sofiapanag/Shipwars-IoT-ESE-516/Code main/Code_main/WINC1500_HTTP_DOWNLOADER_EXAMPLE1/src/IMU/lsm6dso_reg.c

/**
  ******************************************************************************
  * @file    lsm6dso_reg.c
  * @author  Sensors Software Solution Team
  * @brief   LSM6DSO driver file
  ******************************************************************************
  * @attention
  *
  * <h2><center>&copy; Copyright (c) 2021 STMicroelectronics.
  * All rights reserved.</center></h2>
  *
  * This software component is licensed by ST under BSD 3-Clause license,
  * the "License"; You may not use this file except in compliance with the
  * License. You may obtain a copy of the License at:
  *                        opensource.org/licenses/BSD-3-Clause
  *
  ******************************************************************************
  */

#include "lsm6dso_reg.h"
#include "I2cDriver\I2cDriver.h"
#include <stddef.h>

/**
  * @defgroup  LSM6DSO
  * @brief     This file provides a set of functions needed to drive the
  *            lsm6dso enhanced inertial module.
  * @{
  *
  */

/**
  * @defgroup  LSM6DSO_Interfaces_Functions
  * @brief     This section provide a set of functions used to read and
  *            write a generic register of the device.
  *            MANDATORY: return 0 -> no Error.
  * @{
  *
  */

/**
  * @brief  Read generic device register
  *
  * @param  ctx   read / write interface definitions(ptr)
  * @param  reg   register to read
  * @param  data  pointer to buffer that store the data read(ptr)
  * @param  len   number of consecutive register to read
  * @retval          interface status (MANDATORY: return 0 -> no Error)
  *
  */
int32_t lsm6dso_read_reg(stmdev_ctx_t *ctx, uint8_t reg,
                         uint8_t *data,
                         uint16_t len)
{
  int32_t ret;

  ret = ctx->read_reg(ctx->handle, reg, data, len);

  return ret;
}

/**
  * @brief  Write generic device register
  *
  * @param  ctx   read / write interface definitions(ptr)
  * @param  reg   register to write
  * @param  data  pointer to data to write in register reg(ptr)
  * @param  len   number of consecutive register to write
  * @retval          interface status (MANDATORY: return 0 -> no Error)
  *
  */
int32_t lsm6dso_write_reg(stmdev_ctx_t *ctx, uint8_t reg,
                          uint8_t *data,
                          uint16_t len)
{
  int32_t ret;

  ret = ctx->write_reg(ctx->handle, reg, data, len);

  return ret;
}

/**
  * @}
  *
  */

/**
  * @defgroup  LSM6DSOX_Private_functions
  * @brief     Section collect all the utility functions needed by APIs.
  * @{
  *
  */

static void bytecpy(uint8_t *target, uint8_t *source)
{
  if ((target != NULL) && (source != NULL))
  {
    *target = *source;
  }
}

/**
  * @defgroup  LSM6DSO_Sensitivity
  * @brief     These functions convert raw-data into engineering units.
  * @{
  *
  */
float_t lsm6dso_from_fs2_to_mg(int16_t lsb)
{
  return ((float_t)lsb) * 0.061f;
}

float_t lsm6dso_from_fs4_to_mg(int16_t lsb)
{
  return ((float_t)lsb) * 0.122f;
}

float_t lsm6dso_from_fs8_to_mg(int16_t lsb)
{
  return ((float_t)lsb) * 0.244f;
}

float_t lsm6dso_from_fs16_to_mg(int16_t lsb)
{
  return ((float_t)lsb) * 0.488f;
}

float_t lsm6dso_from_fs125_to_mdps(int16_t lsb)
{
  return ((float_t)lsb) * 4.375f;
}

float_t lsm6dso_from_fs500_to_mdps(int16_t lsb)
{
  return ((float_t)lsb) * 17.50f;
}

float_t lsm6dso_from_fs250_to_mdps(int16_t lsb)
{
  return ((float_t)lsb) * 8.750f;
}

float_t lsm6dso_from_fs1000_to_mdps(int16_t lsb)
{
  return ((float_t)lsb) * 35.0f;
}

float_t lsm6dso_from_fs2000_to_mdps(int16_t lsb)
{
  return ((float_t)lsb) * 70.0f;
}

float_t lsm6dso_from_lsb_to_celsius(int16_t lsb)
{
  return (((float_t)lsb / 256.0f) + 25.0f);
}

float_t lsm6dso_from_lsb_to_nsec(int16_t lsb)
{
  return ((float_t)lsb * 25000.0f);
}

/**
  * @}
  *
  */

/**
  * @defgroup  LSM6DSO_Data_Generation
  * @brief     This section groups all the functions concerning
  *            data generation.
  *
  */

/**
  * @brief  Accelerometer full-scale selection.[set]
  *
  * @param  ctx      read / write interface definitions
  * @param  val      change the values of fs_xl in reg CTRL1_XL
  * @retval             interface status (MANDATORY: return 0 -> no Error)
  *
  */
int32_t lsm6dso_xl_full_scale_set(stmdev_ctx_t *ctx,
                                  lsm6dso_fs_xl_t val)
{
  lsm6dso_ctrl1_xl_t reg;
  int32_t ret;

  ret = lsm6dso_read_reg(ctx, LSM6DSO_CTRL1_XL, (uint8_t *)&reg, 1);

  if (ret == 0)
  {
    reg.fs_xl = (uint8_t) val;
    ret = lsm6dso_write_reg(ctx, LSM6DSO_CTRL1_XL, (uint8_t *)&reg, 1);
  }

  return ret;
}

/**
  * @brief  Accelerometer full-scale selection.[get]
  *
  * @param  ctx      read / write interface definitions
  * @param  val      Get the values of fs_xl in reg CTRL1_XL
  * @retval             interface status (MANDATORY: return 0 -> no Error)
  *
  */
int32_t lsm6dso_xl_full_scale_get(stmdev_ctx_t *ctx,
                                  lsm6dso_fs_xl_t *val)
{
  lsm6dso_ctrl1_xl_t reg;
  int32_t ret;

  ret = lsm6dso_read_reg(ctx, LSM6DSO_CTRL1_XL, (uint8_t *)&reg, 1);

  switch (reg.fs_xl)
  {
    case LSM6DSO_2g:
      *val = LSM6DSO_2g;
      break;

    case LSM6DSO_16g:
      *val = LSM6DSO_16g;
      break;

    case LSM6DSO_4g:
      *val = LSM6DSO_4g;
      break;

    case LSM6DSO_8g:
      *val = LSM6DSO_8g;
      break;

    default:
      *val = LSM6DSO_2g;
      break;
  }

  return ret;
}

/**
  * @brief  Accelerometer UI data rate selection.[set]
  *
  * @param  ctx      read / write interface definitions
  * @param  val      change the values of odr_xl in reg CTRL1_XL
  * @retval             interface status (MANDATORY: return 0 -> no Error)
  *
  */
int32_t lsm6dso_xl_data_rate_set(stmdev_ctx_t *ctx,
                                 lsm6dso_odr_xl_t val)
{
  lsm6dso_odr_xl_t odr_xl =  val;
  lsm6dso_emb_fsm_enable_t fsm_enable;
  lsm6dso_fsm_odr_t fsm_odr;
  lsm6dso_ctrl1_xl_t reg;
  int32_t ret;

  /* Check the Finite State Machine data rate constraints */
  ret =  lsm6dso_fsm_enable_get(ctx, &fsm_enable);

  if (ret == 0)
  {
    if ((fsm_enable.fsm_enable_a.fsm1_en  |
         fsm_enable.fsm_enable_a.fsm2_en  |
         fsm_enable.fsm_enable_a.fsm3_en  |
         fsm_enable.fsm_enable_a.fsm4_en  |
         fsm_enable.fsm_enable_a.fsm5_en  |
         fsm_enable.fsm_enable_a.fsm6_en  |
         fsm_enable.fsm_enable_a.fsm7_en  |
         fsm_enable.fsm_enable_a.fsm8_en  |
         fsm_enable.fsm_enable_b.fsm9_en  |
         fsm_enable.fsm_enable_b.fsm10_en |
         fsm_enable.fsm_enable_b.fsm11_en |
         fsm_enable.fsm_enable_b.fsm12_en |
         fsm_enable.fsm_enable_b.fsm13_en |
         fsm_enable.fsm_enable_b.fsm14_en |
         fsm_enable.fsm_enable_b.fsm15_en |
         fsm_enable.fsm_enable_b.fsm16_en) == PROPERTY_ENABLE)
    {
      ret =  lsm6dso_fsm_data_rate_get(ctx, &fsm_odr);

      if (ret == 0)
      {
        switch (fsm_odr)
        {
          case LSM6DSO_ODR_FSM_12Hz5:
            if (val == LSM6DSO_XL_ODR_OFF)
            {
              odr_xl = LSM6DSO_XL_ODR_12Hz5;
            }

            else
            {
              odr_xl = val;
            }

            break;

          case LSM6DSO_ODR_FSM_26Hz:
            if (val == LSM6DSO_XL_ODR_OFF)
            {
              odr_xl = LSM6DSO_XL_ODR_26Hz;
            }

            else if (val == LSM6DSO_XL_ODR_12Hz5)
            {
              odr_xl = LSM6DSO_XL_ODR_26Hz;
            }

            else
            {
              odr_xl = val;
            }

            break;

          case LSM6DSO_ODR_FSM_52Hz:
            if (val == LSM6DSO_XL_ODR_OFF)
            {
              odr_xl = LSM6DSO_XL_ODR_52Hz;
            }

            else if (val == LSM6DSO_XL_ODR_12Hz5)
            {
              odr_xl = LSM6DSO_XL_ODR_52Hz;
            }

            else if (val == LSM6DSO_XL_ODR_26Hz)
            {
              odr_xl = LSM6DSO_XL_ODR_52Hz;
            }

            else
            {
              odr_xl = val;
            }

            break;

          case LSM6DSO_ODR_FSM_104Hz:
            if (val == LSM6DSO_XL_ODR_OFF)
            {
              odr_xl = LSM6DSO_XL_ODR_104Hz;
            }

            else if (val == LSM6DSO_XL_ODR_12Hz5)
            {
              odr_xl = LSM6DSO_XL_ODR_104Hz;
            }

            else if (val == LSM6DSO_XL_ODR_26Hz)
            {
              odr_xl = LSM6DSO_XL_ODR_104Hz;
            }

            else if (val == LSM6DSO_XL_ODR_52Hz)
            {
              odr_xl = LSM6DSO_XL_ODR_104Hz;
            }

            else
            {
              odr_xl = val;
            }

            break;

          default:
            odr_xl = val;
            break;
        }
      }
    }
  }

  if (ret == 0)
  {
    ret = lsm6dso_read_reg(ctx, LSM6DSO_CTRL1_XL, (uint8_t *)&reg, 1);
  }

  if (ret == 0)
  {
    reg.odr_xl = (uint8_t) odr_xl;
    ret = lsm6dso_write_reg(ctx, LSM6DSO_CTRL1_XL, (uint8_t *)&reg, 1);
  }

  return ret;
}

/**
  * @brief  Accelerometer UI data rate selection.[get]
  *
  * @param  ctx      read / write interface definitions
  * @param  val      Get the values of odr_xl in reg CTRL1_XL
  * @retval             interface status (MANDATORY: return 0 -> no Error)
  *
  */
int32_t lsm6dso_xl_data_rate_get(stmdev_ctx_t *ctx,
                                 lsm6dso_odr_xl_t *val)
{
  lsm6dso_ctrl1_xl_t reg;
  int32_t ret;

  ret = lsm6dso_read_reg(ctx, LSM6DSO_CTRL1_XL, (uint8_t *)&reg, 1);

  switch (reg.odr_xl)
  {
    case LSM6DSO_XL_ODR_OFF:
      *val = LSM6DSO_XL_ODR_OFF;
      break;

    case LSM6DSO_XL_ODR_12Hz5:
      *val = LSM6DSO_XL_ODR_12Hz5;
      break;

    case LSM6DSO_XL_ODR_26Hz:
      *val = LSM6DSO_XL_ODR_26Hz;
      break;

    case LSM6DSO_XL_ODR_52Hz:
      *val = LSM6DSO_XL_ODR_52Hz;
      break;

    case LSM6DSO_XL_ODR_104Hz:
      *val = LSM6DSO_XL_ODR_104Hz;
      break;

    case LSM6DSO_XL_ODR_208Hz:
      *val = LSM6DSO_XL_ODR_208Hz;
      break;

    case LSM6DSO_XL_ODR_417Hz:
      *val = LSM6DSO_XL_ODR_417Hz;
      break;

    case LSM6DSO_XL_ODR_833Hz:
      *val = LSM6DSO_XL_ODR_833Hz;
      break;

    case LSM6DSO_XL_ODR_1667Hz:
      *val = LSM6DSO_XL_ODR_1667Hz;
      break;

    case LSM6DSO_XL_ODR_3333Hz:
      *val = LSM6DSO_XL_ODR_3333Hz;
      break;

    case LSM6DSO_XL_ODR_6667Hz:
      *val = LSM6DSO_XL_ODR_6667Hz;
      break;

    case LSM6DSO_XL_ODR_1Hz6:
      *val = LSM6DSO_XL_ODR_1Hz6;
      break;

    default:
      *val = LSM6DSO_XL_ODR_OFF;
      break;
  }

  return ret;
}

/**
  * @brief  Gyroscope UI chain full-scale selection.[set]
  *
  * @param  ctx      read / write interface definitions
  * @param  val      change the values of fs_g in reg CTRL2_G
  * @retval             interface status (MANDATORY: return 0 -> no Error)
  *
  */
int32_t lsm6dso_gy_full_scale_set(stmdev_ctx_t *ctx,
                                  lsm6dso_fs_g_t val)
{
  lsm6dso_ctrl2_g_t reg;
  int32_t ret;

  ret = lsm6dso_read_reg(ctx, LSM6DSO_CTRL2_G, (uint8_t *)&reg, 1);

  if (ret == 0)
  {
    reg.fs_g = (uint8_t) val;
    ret = lsm6dso_write_reg(ctx, LSM6DSO_CTRL2_G, (uint8_t *)&reg, 1);
  }

  return ret;
}

/**
  * @brief  Gyroscope UI chain full-scale selection.[get]
  *
  * @param  ctx      read / write interface definitions
  * @param  val      Get the values of fs_g in reg CTRL2_G
  * @retval             interface status (MANDATORY: return 0 -> no Error)
  *
  */
int32_t lsm6dso_gy_full_scale_get(stmdev_ctx_t *ctx,
                                  lsm6dso_fs_g_t *val)
{
  lsm6dso_ctrl2_g_t reg;
  int32_t ret;

  ret = lsm6dso_read_reg(ctx, LSM6DSO_CTRL2_G, (uint8_t *)&reg, 1);

  switch (reg.fs_g)
  {
    case LSM6DSO_250dps:
      *val = LSM6DSO_250dps;
      break;

    case LSM6DSO_125dps:
      *val = LSM6DSO_125dps;
      break;

    case LSM6DSO_500dps:
      *val = LSM6DSO_500dps;
      break;

    case LSM6DSO_1000dps:
      *val = LSM6DSO_1000dps;
      break;

    case LSM6DSO_2000dps:
      *val = LSM6DSO_2000dps;
      break;

    default:
      *val = LSM6DSO_250dps;
      break;
  }

  return ret;
}

/**
  * @brief  Gyroscope UI data rate selection.[set]
  *
  * @param  ctx      read / write interface definitions
  * @param  val      change the values of odr_g in reg CTRL2_G
  * @retval             interface status (MANDATORY: return 0 -> no Error)
  *
  */
int32_t lsm6dso_gy_data_rate_set(stmdev_ctx_t *ctx,
                                 lsm6dso_odr_g_t val)
{
  lsm6dso_odr_g_t odr_gy =  val;
  lsm6dso_emb_fsm_enable_t fsm_enable;
  lsm6dso_fsm_odr_t fsm_odr;
  lsm6dso_ctrl2_g_t reg;
  int32_t ret;

  /* Check the Finite State Machine data rate constraints */
  ret =  lsm6dso_fsm_enable_get(ctx, &fsm_enable);

  if (ret == 0)
  {
    if ((fsm_enable.fsm_enable_a.fsm1_en  |
         fsm_enable.fsm_enable_a.fsm2_en  |
         fsm_enable.fsm_enable_a.fsm3_en  |
         fsm_enable.fsm_enable_a.fsm4_en  |
         fsm_enable.fsm_enable_a.fsm5_en  |
         fsm_enable.fsm_enable_a.fsm6_en  |
         fsm_enable.fsm_enable_a.fsm7_en  |
         fsm_enable.fsm_enable_a.fsm8_en  |
         fsm_enable.fsm_enable_b.fsm9_en  |
         fsm_enable.fsm_enable_b.fsm10_en |
         fsm_enable.fsm_enable_b.fsm11_en |
         fsm_enable.fsm_enable_b.fsm12_en |
         fsm_enable.fsm_enable_b.fsm13_en |
         fsm_enable.fsm_enable_b.fsm14_en |
         fsm_enable.fsm_enable_b.fsm15_en |
         fsm_enable.fsm_enable_b.fsm16_en) == PROPERTY_ENABLE)
    {
      ret =  lsm6dso_fsm_data_rate_get(ctx, &fsm_odr);

      if (ret == 0)
      {
        switch (fsm_odr)
        {
          case LSM6DSO_ODR_FSM_12Hz5:
            if (val == LSM6DSO_GY_ODR_OFF)
            {
              odr_gy = LSM6DSO_GY_ODR_12Hz5;
            }

            else
            {
              odr_gy = val;
            }

            break;

          case LSM6DSO_ODR_FSM_26Hz:
            if (val == LSM6DSO_GY_ODR_OFF)
            {
              odr_gy = LSM6DSO_GY_ODR_26Hz;
            }

            else if (val == LSM6DSO_GY_ODR_12Hz5)
            {
              odr_gy = LSM6DSO_GY_ODR_26Hz;
            }

            else
            {
              odr_gy = val;
            }

            break;

          case LSM6DSO_ODR_FSM_52Hz:
            if (val == LSM6DSO_GY_ODR_OFF)
            {
              odr_gy = LSM6DSO_GY_ODR_52Hz;
            }

            else if (val == LSM6DSO_GY_ODR_12Hz5)
            {
              odr_gy = LSM6DSO_GY_ODR_52Hz;
            }

            else if (val == LSM6DSO_GY_ODR_26Hz)
            {
              odr_gy = LSM6DSO_GY_ODR_52Hz;
            }

            else
            {
              odr_gy = val;
            }

            break;

          case LSM6DSO_ODR_FSM_104Hz:
            if (val == LSM6DSO_GY_ODR_OFF)
            {
              odr_gy = LSM6DSO_GY_ODR_104Hz;
            }

            else if (val == LSM6DSO_GY_ODR_12Hz5)
            {
              odr_gy = LSM6DSO_GY_ODR_104Hz;
            }

            else if (val == LSM6DSO_GY_ODR_26Hz)
            {
              odr_gy = LSM6DSO_GY_ODR_104Hz;
            }

            else if (val == LSM6DSO_GY_ODR_52Hz)
            {
              odr_gy = LSM6DSO_GY_ODR_104Hz;
            }

            else
            {
              odr_gy = val;
            }

            break;

          default:
            odr_gy = val;
            break;
        }
      }
    }
  }

  if (ret == 0)
  {
    ret = lsm6dso_read_reg(ctx, LSM6DSO_CTRL2_G, (uint8_t *)&reg, 1);
  }

  if (ret == 0)
  {
    reg.odr_g = (uint8_t) odr_gy;
    ret = lsm6dso_write_reg(ctx, LSM6DSO_CTRL2_G, (uint8_t *)&reg, 1);
  }

  return ret;
}

/**
  * @brief  Gyroscope UI data rate selection.[get]
  *
  * @param  ctx      read / write interface definitions
  * @param  val      Get the values of odr_g in reg CTRL2_G
  * @retval             interface status (MANDATORY: return 0 -> no Error)
  *
  */
int32_t lsm6dso_gy_data_rate_get(stmdev_ctx_t *ctx,
                                 lsm6dso_odr_g_t *val)
{
  lsm6dso_ctrl2_g_t reg;
  int32_t ret;

  ret = lsm6dso_read_reg(ctx, LSM6DSO_CTRL2_G, (uint8_t *)&reg, 1);

  switch (reg.odr_g)
  {
    case LSM6DSO_GY_ODR_OFF:
      *val = LSM6DSO_GY_ODR_OFF;
      break;

    case LSM6DSO_GY_ODR_12Hz5:
      *val = LSM6DSO_GY_ODR_12Hz5;
      break;

    case LSM6DSO_GY_ODR_26Hz:
      *val = LSM6DSO_GY_ODR_26Hz;
      break;

    case LSM6DSO_GY_ODR_52Hz:
      *val = LSM6DSO_GY_ODR_52Hz;
      break;

    case LSM6DSO_GY_ODR_104Hz:
      *val = LSM6DSO_GY_ODR_104Hz;
      break;

    case LSM6DSO_GY_ODR_208Hz:
      *val = LSM6DSO_GY_ODR_208Hz;
      break;

    case LSM6DSO_GY_ODR_417Hz:
      *val = LSM6DSO_GY_ODR_417Hz;
      break;

    case LSM6DSO_GY_ODR_833Hz:
      *val = LSM6DSO_GY_ODR_833Hz;
      break;

    case LSM6DSO_GY_ODR_1667Hz:
      *val = LSM6DSO_GY_ODR_1667Hz;
      break;

    case LSM6DSO_GY_ODR_3333Hz:
      *val = LSM6DSO_GY_ODR_3333Hz;
      break;

    case LSM6DSO_GY_ODR_6667Hz:
      *val = LSM6DSO_GY_ODR_6667Hz;
      break;

    default:
      *val = LSM6DSO_GY_ODR_OFF;
      break;
  }

  return ret;
}

/**
  * @brief  Block data update.[set]
  *
  * @param  ctx      read / write interface definitions
  * @param  val      change the values of bdu in reg CTRL3_C
  * @retval             interface status (MANDATORY: return 0 -> no Error)
  *
  */
int32_t lsm6dso_block_data_update_set(stmdev_ctx_t *ctx, uint8_t val)
{
  lsm6dso_ctrl3_c_t reg;
  int32_t ret;

  ret = lsm6dso_read_reg(ctx, LSM6DSO_CTRL3_C, (uint8_t *)&reg, 1);

  if (ret == 0)
  {
    reg.bdu = val;
    ret = lsm6dso_write_reg(ctx, LSM6DSO_CTRL3_C, (uint8_t *)&reg, 1);
  }

  return ret;
}

/**
  * @brief  Block data update.[get]
  *
  * @param  ctx      read / write interface definitions
  * @param  val      change the values of bdu in reg CTRL3_C
  * @retval             interface status (MANDATORY: return 0 -> no Error)
  *
  */
int32_t lsm6dso_block_data_update_get(stmdev_ctx_t *ctx, uint8_t *val)
{
  lsm6dso_ctrl3_c_t reg;
  int32_t ret;

  ret = lsm6dso_read_reg(ctx, LSM6DSO_CTRL3_C, (uint8_t *)&reg, 1);
  *val = reg.bdu;

  return ret;
}

/**
  * @brief  Weight of XL user offset bits of registers X_OFS_USR (73h),
  *         Y_OFS_USR (74h), Z_OFS_USR (75h).[set]
  *
  * @param  ctx      read / write interface definitions
  * @param  val      change the values of usr_off_w in reg CTRL6_C
  * @retval             interface status (MANDATORY: return 0 -> no Error)
  *
  */
int32_t lsm6dso_xl_offset_weight_set(stmdev_ctx_t *ctx,
                                     lsm6dso_usr_off_w_t val)
{
  lsm6dso_ctrl6_c_t reg;
  int32_t ret;

  ret = lsm6dso_read_reg(ctx, LSM6DSO_CTRL6_C, (uint8_t *)&reg, 1);

  if (ret == 0)
  {
    reg.usr_off_w = (uint8_t)val;
    ret = lsm6dso_write_reg(ctx, LSM6DSO_CTRL6_C, (uint8_t *)&reg, 1);
  }

  return ret;
}

/**
  * @brief    Weight of XL user offset bits of registers X_OFS_USR (73h),
  *           Y_OFS_USR (74h), Z_OFS_USR (75h).[get]
  *
  * @param    ctx      read / write interface definitions
  * @param    val      Get the values of usr_off_w in reg CTRL6_C
  * @retval             interface status (MANDATORY: return 0 -> no Error)
  *
  */
int32_t lsm6dso_xl_offset_weight_get(stmdev_ctx_t *ctx,
                                     lsm6dso_usr_off_w_t *val)
{
  lsm6dso_ctrl6_c_t reg;
  int32_t ret;

  ret = lsm6dso_read_reg(ctx, LSM6DSO_CTRL6_C, (uint8_t *)&reg, 1);

  switch (reg.usr_off_w)
  {
    case LSM6DSO_LSb_1mg:
      *val = LSM6DSO_LSb_1mg;
      break;

    case LSM6DSO_LSb_16mg:
      *val = LSM6DSO_LSb_16mg;
      break;

    default:
      *val = LSM6DSO_LSb_1mg;
      break;
  }

  return ret;
}

/**
  * @brief  Accelerometer power mode.[set]
  *
  * @param  ctx      read / write interface definitions
  * @param  val      change the values of xl_hm_mode in
  *                               reg CTRL6_C
  * @retval             interface status (MANDATORY: return 0 -> no Error)
  *
  */
int32_t lsm6dso_xl_power_mode_set(stmdev_ctx_t *ctx,
                                  lsm6dso_xl_hm_mode_t val)
{
  lsm6dso_ctrl5_c_t ctrl5_c;
  lsm6dso_ctrl6_c_t ctrl6_c;
  int32_t ret;

  ret = lsm6dso_read_reg(ctx, LSM6DSO_CTRL5_C, (uint8_t *) &ctrl5_c, 1);

  if (ret == 0)
  {
    ctrl5_c.xl_ulp_en = ((uint8_t)val & 0x02U) >> 1;
    ret = lsm6dso_write_reg(ctx, LSM6DSO_CTRL5_C, (uint8_t *) &ctrl5_c, 1);
  }

  if (ret == 0)
  {
    ret = lsm6dso_read_reg(ctx, LSM6DSO_CTRL6_C, (uint8_t *) &ctrl6_c, 1);
  }

  if (ret == 0)
  {
    ctrl6_c.xl_hm_mode = (uint8_t)val & 0x01U;
    ret = lsm6dso_write_reg(ctx, LSM6DSO_CTRL6_C, (uint8_t *) &ctrl6_c, 1);
  }

  return ret;
}

/**
  * @brief  Accelerometer power mode.[get]
  *
  * @param  ctx      read / write interface definitions
  * @param  val      Get the values of xl_hm_mode in reg CTRL6_C
  * @retval             interface status (MANDATORY: return 0 -> no Error)
  *
  */
int32_t lsm6dso_xl_power_mode_get(stmdev_ctx_t *ctx,
                                  lsm6dso_xl_hm_mode_t *val)
{
  lsm6dso_ctrl5_c_t ctrl5_c;
  lsm6dso_ctrl6_c_t ctrl6_c;
  int32_t ret;

  ret = lsm6dso_read_reg(ctx, LSM6DSO_CTRL5_C, (uint8_t *) &ctrl5_c, 1);

  if (ret == 0)
  {
    ret = lsm6dso_read_reg(ctx, LSM6DSO_CTRL6_C, (uint8_t *) &ctrl6_c, 1);

    switch ((ctrl5_c.xl_ulp_en << 1) | ctrl6_c.xl_hm_mode)
    {
      case LSM6DSO_HIGH_PERFORMANCE_MD:
        *val = LSM6DSO_HIGH_PERFORMANCE_MD;
        break;

      case LSM6DSO_LOW_NORMAL_POWER_MD:
        *val = LSM6DSO_LOW_NORMAL_POWER_MD;
        break;

      case LSM6DSO_ULTRA_LOW_POWER_MD:
        *val = LSM6DSO_ULTRA_LOW_POWER_MD;
        break;

      default:
        *val = LSM6DSO_HIGH_PERFORMANCE_MD;
        break;
    }
  }

  return ret;
}

/**
  * @brief  Operating mode for gyroscope.[set]
  *
  * @param  ctx      read / write interface definitions
  * @param  val      change the values of g_hm_mode in reg CTRL7_G
  * @retval             interface status (MANDATORY: return 0 -> no Error)
  *
  */
int32_t lsm6dso_gy_power_mode_set(stmdev_ctx_t *ctx,
                                  lsm6dso_g_hm_mode_t val)
{
  lsm6dso_ctrl7_g_t reg;
  int32_t ret;

  ret = lsm6dso_read_reg(ctx, LSM6DSO_CTRL7_G, (uint8_t *)&reg, 1);

  if (ret == 0)
  {
    reg.g_hm_mode = (uint8_t)val;
    ret = lsm6dso_write_reg(ctx, LSM6DSO_CTRL7_G, (uint8_t *)&reg, 1);
  }

  return ret;
}

/**
  * @brief  Operating mode for gyroscope.[get]
  *
  * @param  ctx      read / write interface definitions
  * @param  val      Get the values of g_hm_mode in reg CTRL7_G
  * @retval             interface status (MANDATORY: return 0 -> no Error)
  *
  */
int32_t lsm6dso_gy_power_mode_get(stmdev_ctx_t *ctx,
                                  lsm6dso_g_hm_mode_t *val)
{
  lsm6dso_ctrl7_g_t reg;
  int32_t ret;

  ret = lsm6dso_read_reg(ctx, LSM6DSO_CTRL7_G, (uint8_t *)&reg, 1);

  switch (reg.g_hm_mode)
  {
    case LSM6DSO_GY_HIGH_PERFORMANCE:
      *val = LSM6DSO_GY_HIGH_PERFORMANCE;
      break;

    case LSM6DSO_GY_NORMAL:
      *val = LSM6DSO_GY_NORMAL;
      break;

    default:
      *val = LSM6DSO_GY_HIGH_PERFORMANCE;
      break;
  }

  return ret;
}

/**
  * @brief  The STATUS_REG register is read by the primary interface.[get]
  *
  * @param  ctx      read / write interface definitions
  * @param  val      register STATUS_REG
  * @retval             interface status (MANDATORY: return 0 -> no Error)
  *
  */
int32_t lsm6dso_status_reg_get(stmdev_ctx_t *ctx,
                               lsm6dso_status_reg_t *val)
{
  int32_t ret;

  ret = lsm6dso_read_reg(ctx, LSM6DSO_STATUS_REG, (uint8_t *) val, 1);

  return ret;
}

/**
  * @brief  Accelerometer new data available.[get]
  *
  * @param  ctx      read / write interface definitions
  * @param  val      change the values of xlda in reg STATUS_REG
  * @retval             interface status (MANDATORY: return 0 -> no Error)
  *
  */
int32_t lsm6dso_xl_flag_data_ready_get(stmdev_ctx_t *ctx,
                                       uint8_t *val)
{
  lsm6dso_status_reg_t reg;
  int32_t ret;

  ret = lsm6dso_read_reg(ctx, LSM6DSO_STATUS_REG, (uint8_t *)&reg, 1);
  *val = reg.xlda;

  return ret;
}

/**
  * @brief  Gyroscope new data available.[get]
  *
  * @param  ctx      read / write interface definitions
  * @param  val      change the values of gda in reg STATUS_REG
  * @retval             interface status (MANDATORY: return 0 -> no Error)
  *
  */
int32_t lsm6dso_gy_flag_data_ready_get(stmdev_ctx_t *ctx,
                                       uint8_t *val)
{
  lsm6dso_status_reg_t reg;
  int32_t ret;

  ret = lsm6dso_read_reg(ctx, LSM6DSO_STATUS_REG, (uint8_t *)&reg, 1);
  *val = reg.gda;

  return ret;
}

/**
  * @brief  Temperature new data available.[get]
  *
  * @param  ctx      read / write interface definitions
  * @param  val      change the values of tda in reg STATUS_REG
  * @retval             interface status (MANDATORY: return 0 -> no Error)
  *
  */
int32_t lsm6dso_temp_flag_data_ready_get(stmdev_ctx_t *ctx,
                                         uint8_t *val)
{
  lsm6dso_status_reg_t reg;
  int32_t ret;

  ret = lsm6dso_read_reg(ctx, LSM6DSO_STATUS_REG, (uint8_t *)&reg, 1);
  *val = reg.tda;

  return ret;
}

/**
  * @brief  Accelerometer X-axis user offset correction expressed in
  *         two’s complement, weight depends on USR_OFF_W in CTRL6_C (15h).
  *         The value must be in the range [-127 127].[set]
  *
  * @param  ctx      read / write interface definitions
  * @param  buff     buffer that contains data to write
  * @retval             interface status (MANDATORY: return 0 -> no Error)
  *
  */
int32_t lsm6dso_xl_usr_offset_x_set(stmdev_ctx_t *ctx, uint8_t *buff)
{
  int32_t ret;

  ret = lsm6dso_write_reg(ctx, LSM6DSO_X_OFS_USR, buff, 1);

  return ret;
}

/**
  * @brief  Accelerometer X-axis user offset correction expressed in two’s
  *         complement, weight depends on USR_OFF_W in CTRL6_C (15h).
  *         The value must be in the range [-127 127].[get]
  *
  * @param  ctx      read / write interface definitions
  * @param  buff     buffer that stores data read
  * @retval             interface status (MANDATORY: return 0 -> no Error)
  *
  */
int32_t lsm6dso_xl_usr_offset_x_get(stmdev_ctx_t *ctx, uint8_t *buff)
{
  int32_t ret;

  ret = lsm6dso_read_reg(ctx, LSM6DSO_X_OFS_USR, buff, 1);

  return ret;
}

/**
  * @brief  Accelerometer Y-axis user offset correction expressed in two’s
  *         complement, weight depends on USR_OFF_W in CTRL6_C (15h).
  *         The value must be in the range [-127 127].[set]
  *
  * @param  ctx      read / write interface definitions
  * @param  buff     buffer that contains data to write
  * @retval             interface status (MANDATORY: return 0 -> no Error)
  *
  */
int32_t lsm6dso_xl_usr_offset_y_set(stmdev_ctx_t *ctx, uint8_t *buff)
{
  int32_t ret;

  ret = lsm6dso_write_reg(ctx, LSM6DSO_Y_OFS_USR, buff, 1);

  return ret;
}

/**
  * @brief  Accelerometer Y-axis user offset correction expressed in two’s
  *         complement, weight depends on USR_OFF_W in CTRL6_C (15h).
  *         The value must be in the range [-127 127].[get]
  *
  * @param  ctx      read / write interface definitions
  * @param  buff     buffer that stores data read
  * @retval             interface status (MANDATORY: return 0 -> no Error)
  *
  */
int32_t lsm6dso_xl_usr_offset_y_get(stmdev_ctx_t *ctx, uint8_t *buff)
{
  int32_t ret;

  ret = lsm6dso_read_reg(ctx, LSM6DSO_Y_OFS_USR, buff, 1);

  return ret;
}

/**
  * @brief  Accelerometer Z-axis user offset correction expressed in two’s
  *         complement, weight depends on USR_OFF_W in CTRL6_C (15h).
  *         The value must be in the range [-127 127].[set]
  *
  * @param  ctx      read / write interface definitions
  * @param  buff     buffer that contains data to write
  * @retval             interface status (MANDATORY: return 0 -> no Error)
  *
  */
int32_t lsm6dso_xl_usr_offset_z_set(stmdev_ctx_t *ctx, uint8_t *buff)
{
  int32_t ret;

  ret = lsm6dso_write_reg(ctx, LSM6DSO_Z_OFS_USR, buff, 1);

  return ret;
}

/**
  * @brief  Accelerometer Z-axis user offset correction expressed in two’s
  *         complement, weight depends on USR_OFF_W in CTRL6_C (15h).
  *         The value must be in the range [-127 127].[get]
  *
  * @param  ctx      read / write interface definitions
  * @param  buff     buffer that stores data read
  * @retval             interface status (MANDATORY: return 0 -> no Error)
  *
  */
int32_t lsm6dso_xl_usr_offset_z_get(stmdev_ctx_t *ctx, uint8_t *buff)
{
  int32_t ret;

  ret = lsm6dso_read_reg(ctx, LSM6DSO_Z_OFS_USR, buff, 1);

  return ret;
}

/**
  * @brief  Enables user offset on out.[set]
  *
  * @param  ctx      read / write interface definitions
  * @param  val      change the values of usr_off_on_out in reg CTRL7_G
  * @retval             interface status (MANDATORY: return 0 -> no Error)
  *
  */
int32_t lsm6dso_xl_usr_offset_set(stmdev_ctx_t *ctx, uint8_t val)
{
  lsm6dso_ctrl7_g_t reg;
  int32_t ret;

  ret = lsm6dso_read_reg(ctx, LSM6DSO_CTRL7_G, (uint8_t *)&reg, 1);

  if (ret == 0)
  {
    reg.usr_off_on_out = val;
    ret = lsm6dso_write_reg(ctx, LSM6DSO_CTRL7_G, (uint8_t *)&reg, 1);
  }

  return ret;
}

/**
  * @brief  User offset on out flag.[get]
  *
  * @param  ctx      read / write interface definitions
  * @param  val      values of usr_off_on_out in reg CTRL7_G
  * @retval             interface status (MANDATORY: return 0 -> no Error)
  *
  */
int32_t lsm6dso_xl_usr_offset_get(stmdev_ctx_t *ctx, uint8_t *val)
{
  lsm6dso_ctrl7_g_t reg;
  int32_t ret;

  ret = lsm6dso_read_reg(ctx, LSM6DSO_CTRL7_G, (uint8_t *)&reg, 1);
  *val = reg.usr_off_on_out;

  return ret;
}

/**
  * @}
  *
  */

/**
  * @defgroup  LSM6DSO_Timestamp
  * @brief     This section groups all the functions that manage the
  *            timestamp generation.
  * @{
  *
  */

/**
  * @brief  Reset timestamp counter.[set]
  *
  * @param  ctx    Read / write interface definitions.(ptr)
  * @retval        Interface status (MANDATORY: return 0 -> no Error)
  *
  */
int32_t lsm6dso_timestamp_rst(stmdev_ctx_t *ctx)
{
  uint8_t rst_val = 0xAA;
  return lsm6dso_write_reg(ctx, LSM6DSO_TIMESTAMP2, &rst_val, 1);
}

/**
  * @brief  Enables timestamp counter.[set]
  *
  * @param  ctx      read / write interface definitions
  * @param  val      change the values of timestamp_en in reg CTRL10_C
  * @retval             interface status (MANDATORY: return 0 -> no Error)
  *
  */
int32_t lsm6dso_timestamp_set(stmdev_ctx_t *ctx, uint8_t val)
{
  lsm6dso_ctrl10_c_t reg;
  int32_t ret;

  ret = lsm6dso_read_reg(ctx, LSM6DSO_CTRL10_C, (uint8_t *)&reg, 1);

  if (ret == 0)
  {
    reg.timestamp_en = val;
    ret = lsm6dso_write_reg(ctx, LSM6DSO_CTRL10_C, (uint8_t *)&reg, 1);
  }

  return ret;
}

/**
  * @brief  Enables timestamp counter.[get]
  *
  * @param  ctx      read / write interface definitions
  * @param  val      change the values of timestamp_en in reg CTRL10_C
  * @retval             interface status (MANDATORY: return 0 -> no Error)
  *
  */
int32_t lsm6dso_timestamp_get(stmdev_ctx_t *ctx, uint8_t *val)
{
  lsm6dso_ctrl10_c_t reg;
  int32_t ret;

  ret = lsm6dso_read_reg(ctx, LSM6DSO_CTRL10_C, (uint8_t *)&reg, 1);
  *val = reg.timestamp_en;

  return ret;
}

/**
  * @brief  Timestamp first data output register (r).
  *         The value is expressed as a 32-bit word and the bit
  *         resolution is 25 μs.[get]
  *
  * @param  ctx      read / write interface definitions
  * @param  buff     buffer that stores data read
  * @retval             interface status (MANDATORY: return 0 -> no Error)
  *
  */
int32_t lsm6dso_timestamp_raw_get(stmdev_ctx_t *ctx, uint32_t *val)
{
  uint8_t buff[4];
  int32_t ret;

  ret = lsm6dso_read_reg(ctx, LSM6DSO_TIMESTAMP0, buff, 4);
  *val = buff[3];
  *val = (*val * 256U) +  buff[2];
  *val = (*val * 256U) +  buff[1];
  *val = (*val * 256U) +  buff[0];

  return ret;
}

/**
  * @}
  *
  */

/**
  * @defgroup  LSM6DSO_Data output
  * @brief     This section groups all the data output functions.
  * @{
  *
  */

/**
  * @brief  Circular burst-mode (rounding) read of the output
  *         registers.[set]
  *
  * @param  ctx      read / write interface definitions
  * @param  val      change the values of rounding in reg CTRL5_C
  * @retval             interface status (MANDATORY: return 0 -> no Error)
  *
  */
int32_t lsm6dso_rounding_mode_set(stmdev_ctx_t *ctx,
                                  lsm6dso_rounding_t val)
{
  lsm6dso_ctrl5_c_t reg;
  int32_t ret;

  ret = lsm6dso_read_reg(ctx, LSM6DSO_CTRL5_C, (uint8_t *)&reg, 1);

  if (ret == 0)
  {
    reg.rounding = (uint8_t)val;
    ret = lsm6dso_write_reg(ctx, LSM6DSO_CTRL5_C, (uint8_t *)&reg, 1);
  }

  return ret;
}

/**
  * @brief  Gyroscope UI chain full-scale selection.[get]
  *
  * @param  ctx      read / write interface definitions
  * @param  val      Get the values of rounding in reg CTRL5_C
  * @retval             interface status (MANDATORY: return 0 -> no Error)
  *
  */
int32_t lsm6dso_rounding_mode_get(stmdev_ctx_t *ctx,
                                  lsm6dso_rounding_t *val)
{
  lsm6dso_ctrl5_c_t reg;
  int32_t ret;

  ret = lsm6dso_read_reg(ctx, LSM6DSO_CTRL5_C, (uint8_t *)&reg, 1);

  switch (reg.rounding)
  {
    case LSM6DSO_NO_ROUND:
      *val = LSM6DSO_NO_ROUND;
      break;

    case LSM6DSO_ROUND_XL:
      *val = LSM6DSO_ROUND_XL;
      break;

    case LSM6DSO_ROUND_GY:
      *val = LSM6DSO_ROUND_GY;
      break;

    case LSM6DSO_ROUND_GY_XL:
      *val = LSM6DSO_ROUND_GY_XL;
      break;

    default:
      *val = LSM6DSO_NO_ROUND;
      break;
  }

  return ret;
}

/**
  * @brief  Temperature data output register (r).
  *         L and H registers together express a 16-bit word in two’s
  *         complement.[get]
  *
  * @param  ctx      read / write interface definitions
  * @param  buff     buffer that stores data read
  * @retval             interface status (MANDATORY: return 0 -> no Error)
  *
  */
int32_t lsm6dso_temperature_raw_get(stmdev_ctx_t *ctx, int16_t *val)
{
  uint8_t buff[2];
  int32_t ret;

  ret = lsm6dso_read_reg(ctx, LSM6DSO_OUT_TEMP_L, buff, 2);
  val[0] = (int16_t)buff[1];
  val[0] = (val[0] * 256) + (int16_t)buff[0];

  return ret;
}

/**
  * @brief  Angular rate sensor. The value is expressed as a 16-bit
  *         word in two’s complement.[get]
  *
  * @param  ctx      read / write interface definitions
  * @param  buff     buffer that stores data read
  * @retval             interface status (MANDATORY: return 0 -> no Error)
  *
  */
int32_t lsm6dso_angular_rate_raw_get(stmdev_ctx_t *ctx, int16_t *val)
{
  uint8_t buff[6];
  int32_t ret;

  ret = lsm6dso_read_reg(ctx, LSM6DSO_OUTX_L_G, buff, 6);
  val[0] = (int16_t)buff[1];
  val[0] = (val[0] * 256) + (int16_t)buff[0];
  val[1] = (int16_t)buff[3];
  val[1] = (val[1] * 256) + (int16_t)buff[2];
  val[2] = (int16_t)buff[5];
  val[2] = (val[2] * 256) + (int16_t)buff[4];

  return ret;
}

/**
  * @brief  Linear acceleration output register.
  *         The value is expressed as a 16-bit word in two’s complement.[get]
  *
  * @param  ctx      read / write interface definitions
  * @param  buff     buffer that stores data read
  * @retval             interface status (MANDATORY: return 0 -> no Error)
  *
  */
int32_t lsm6dso_acceleration_raw_get(stmdev_ctx_t *ctx, int16_t *val)
{
  uint8_t buff[6];
  int32_t ret;

  ret = lsm6dso_read_reg(ctx, LSM6DSO_OUTX_L_A, buff, 6);
  val[0] = (int16_t)buff[1];
  val[0] = (val[0] * 256) + (int16_t)buff[0];
  val[1] = (int16_t)buff[3];
  val[1] = (val[1] * 256) + (int16_t)buff[2];
  val[2] = (int16_t)buff[5];
  val[2] = (val[2] * 256) + (int16_t)buff[4];

  return ret;
}

/**
  * @brief  FIFO data output [get]
  *
  * @param  ctx      read / write interface definitions
  * @param  buff     buffer that stores data read
  * @retval             interface status (MANDATORY: return 0 -> no Error)
  *
  */
int32_t lsm6dso_fifo_out_raw_get(stmdev_ctx_t *ctx, uint8_t *buff)
{
  int32_t ret;

  ret = lsm6dso_read_reg(ctx, LSM6DSO_FIFO_DATA_OUT_X_L, buff, 6);

  return ret;
}

/**
  * @brief  Step counter output register.[get]
  *
  * @param  ctx      read / write interface definitions
  * @param  buff     buffer that stores data read
  * @retval             interface status (MANDATORY: return 0 -> no Error)
  *
  */
int32_t lsm6dso_number_of_steps_get(stmdev_ctx_t *ctx, uint16_t *val)
{
  uint8_t buff[2];
  int32_t ret;

  ret = lsm6dso_mem_bank_set(ctx, LSM6DSO_EMBEDDED_FUNC_BANK);

  if (ret == 0)
  {
    ret = lsm6dso_read_reg(ctx, LSM6DSO_STEP_COUNTER_L, buff, 2);
  }

  if (ret == 0)
  {
    *val = buff[1];
    *val = (*val * 256U) +  buff[0];
    ret = lsm6dso_mem_bank_set(ctx, LSM6DSO_USER_BANK);
  }

  return ret;
}

/**
  * @brief  Reset step counter register.[get]
  *
  * @param  ctx      read / write interface definitions
  * @retval             interface status (MANDATORY: return 0 -> no Error)
  *
  */
int32_t lsm6dso_steps_reset(stmdev_ctx_t *ctx)
{
  lsm6dso_emb_func_src_t reg;
  int32_t ret;

  ret = lsm6dso_mem_bank_set(ctx, LSM6DSO_EMBEDDED_FUNC_BANK);

  if (ret == 0)
  {
    ret = lsm6dso_read_reg(ctx, LSM6DSO_EMB_FUNC_SRC, (uint8_t *)&reg, 1);
  }

  if (ret == 0)
  {
    reg.pedo_rst_step = PROPERTY_ENABLE;
    ret = lsm6dso_write_reg(ctx, LSM6DSO_EMB_FUNC_SRC, (uint8_t *)&reg, 1);
  }

  if (ret == 0)
  {
    ret = lsm6dso_mem_bank_set(ctx, LSM6DSO_USER_BANK);
  }

  return ret;
}

/**
  * @}
  *
  */

/**
  * @defgroup  LSM6DSO_common
  * @brief   This section groups common useful functions.
  * @{
  *
  */

/**
  * @brief  Difference in percentage of the effective ODR(and timestamp rate)
  *         with respect to the typical.
  *         Step:  0.15%. 8-bit format, 2's complement.[set]
  *
  * @param  ctx      read / write interface definitions
  * @param  val      change the values of freq_fine in reg
  *                      INTERNAL_FREQ_FINE
  * @retval             interface status (MANDATORY: return 0 -> no Error)
  *
  */
int32_t lsm6dso_odr_cal_reg_set(stmdev_ctx_t *ctx, uint8_t val)
{
  lsm6dso_internal_freq_fine_t reg;
  int32_t ret;

  ret = lsm6dso_read_reg(ctx, LSM6DSO_INTERNAL_FREQ_FINE,
                         (uint8_t *)&reg, 1);

  if (ret == 0)
  {
    reg.freq_fine = val;
    ret = lsm6dso_write_reg(ctx, LSM6DSO_INTERNAL_FREQ_FINE,
                            (uint8_t *)&reg, 1);
  }

  return ret;
}

/**
  * @brief  Difference in percentage of the effective ODR(and timestamp rate)
  *         with respect to the typical.
  *         Step:  0.15%. 8-bit format, 2's complement.[get]
  *
  * @param  ctx      read / write interface definitions
  * @param  val      change the values of freq_fine in reg INTERNAL_FREQ_FINE
  * @retval             interface status (MANDATORY: return 0 -> no Error)
  *
  */
int32_t lsm6dso_odr_cal_reg_get(stmdev_ctx_t *ctx, uint8_t *val)
{
  lsm6dso_internal_freq_fine_t reg;
  int32_t ret;

  ret = lsm6dso_read_reg(ctx, LSM6DSO_INTERNAL_FREQ_FINE,
                         (uint8_t *)&reg, 1);
  *val = reg.freq_fine;

  return ret;
}


/**
  * @brief  Enable access to the embedded functions/sensor
  *         hub configuration registers.[set]
  *
  * @param  ctx      read / write interface definitions
  * @param  val      change the values of reg_access in
  *                               reg FUNC_CFG_ACCESS
  * @retval             interface status (MANDATORY: return 0 -> no Error)
  *
  */
int32_t lsm6dso_mem_bank_set(stmdev_ctx_t *ctx,
                             lsm6dso_reg_access_t val)
{
  lsm6dso_func_cfg_access_t reg;
  int32_t ret;

  ret = lsm6dso_read_reg(ctx, LSM6DSO_FUNC_CFG_ACCESS, (uint8_t *)&reg, 1);

  if (ret == 0)
  {
    reg.reg_access = (uint8_t)val;
    ret = lsm6dso_write_reg(ctx, LSM6DSO_FUNC_CFG_ACCESS, (uint8_t *)&reg, 1);
  }

  return ret;
}

/**
  * @brief  Enable access to the embedded functions/sensor
  *         hub configuration registers.[get]
  *
  * @param  ctx      read / write interface definitions
  * @param  val      Get the values of reg_access in
  *                               reg FUNC_CFG_ACCESS
  * @retval             interface status (MANDATORY: return 0 -> no Error)
  *
  */
int32_t lsm6dso_mem_bank_get(stmdev_ctx_t *ctx,
                             lsm6dso_reg_access_t *val)
{
  lsm6dso_func_cfg_access_t reg;
  int32_t ret;

  ret = lsm6dso_read_reg(ctx, LSM6DSO_FUNC_CFG_ACCESS, (uint8_t *)&reg, 1);

  switch (reg.reg_access)
  {
    case LSM6DSO_USER_BANK:
      *val = LSM6DSO_USER_BANK;
      break;

    case LSM6DSO_SENSOR_HUB_BANK:
      *val = LSM6DSO_SENSOR_HUB_BANK;
      break;

    case LSM6DSO_EMBEDDED_FUNC_BANK:
      *val = LSM6DSO_EMBEDDED_FUNC_BANK;
      break;

    default:
      *val = LSM6DSO_USER_BANK;
      break;
  }

  return ret;
}

/**
  * @brief  Write a line(byte) in a page.[set]
  *
  * @param  ctx      read / write interface definitions
  * @param  uint8_t address: page line address
  * @param  val      value to write
  * @retval             interface status (MANDATORY: return 0 -> no Error)
  *
  */
int32_t lsm6dso_ln_pg_write_byte(stmdev_ctx_t *ctx, uint16_t address,
                                 uint8_t *val)
{
  lsm6dso_page_rw_t page_rw;
  lsm6dso_page_sel_t page_sel;
  lsm6dso_page_address_t page_address;
  int32_t ret;

  ret = lsm6dso_mem_bank_set(ctx, LSM6DSO_EMBEDDED_FUNC_BANK);

  if (ret == 0)
  {
    ret = lsm6dso_read_reg(ctx, LSM6DSO_PAGE_RW, (uint8_t *) &page_rw, 1);
  }

  if (ret == 0)
  {
    page_rw.page_rw = 0x02; /* page_write enable */
    ret = lsm6dso_write_reg(ctx, LSM6DSO_PAGE_RW, (uint8_t *) &page_rw, 1);
  }

  if (ret == 0)
  {
    ret = lsm6dso_read_reg(ctx, LSM6DSO_PAGE_SEL, (uint8_t *) &page_sel, 1);
  }

  if (ret == 0)
  {
    page_sel.page_sel = ((uint8_t)(address >> 8) & 0x0FU);
    page_sel.not_used_01 = 1;
    ret = lsm6dso_write_reg(ctx, LSM6DSO_PAGE_SEL, (uint8_t *) &page_sel, 1);
  }

  if (ret == 0)
  {
    page_address.page_addr = (uint8_t)address & 0xFFU;
    ret = lsm6dso_write_reg(ctx, LSM6DSO_PAGE_ADDRESS,
                            (uint8_t *)&page_address, 1);
  }

  if (ret == 0)
  {
    ret = lsm6dso_write_reg(ctx, LSM6DSO_PAGE_VALUE, val, 1);
  }

  if (ret == 0)
  {
    ret = lsm6dso_read_reg(ctx, LSM6DSO_PAGE_RW, (uint8_t *) &page_rw, 1);
  }

  if (ret == 0)
  {
    page_rw.page_rw = 0x00; /* page_write disable */
    ret = lsm6dso_write_reg(ctx, LSM6DSO_PAGE_RW, (uint8_t *) &page_rw, 1);
  }

  if (ret == 0)
  {
    ret = lsm6dso_mem_bank_set(ctx, LSM6DSO_USER_BANK);
  }

  return ret;
}

/**
  * @brief  Write buffer in a page.[set]
  *
  * @param  ctx      read / write interface definitions
  * @param  uint8_t address: page line address
  * @param  uint8_t *buf: buffer to write
  * @param  uint8_t len: buffer len
  * @retval             interface status (MANDATORY: return 0 -> no Error)
  *
  */
int32_t lsm6dso_ln_pg_write(stmdev_ctx_t *ctx, uint16_t address,
                            uint8_t *buf, uint8_t len)
{
  lsm6dso_page_rw_t page_rw;
  lsm6dso_page_sel_t page_sel;
  lsm6dso_page_address_t  page_address;
  uint16_t addr_pointed;
  int32_t ret;

  uint8_t i ;
  addr_pointed = address;
  ret = lsm6dso_mem_bank_set(ctx, LSM6DSO_EMBEDDED_FUNC_BANK);

  if (ret == 0)
  {
    ret = lsm6dso_read_reg(ctx, LSM6DSO_PAGE_RW, (uint8_t *) &page_rw, 1);
  }

  if (ret == 0)
  {
    page_rw.page_rw = 0x02; /* page_write enable*/
    ret = lsm6dso_write_reg(ctx, LSM6DSO_PAGE_RW, (uint8_t *) &page_rw, 1);
  }

  if (ret == 0)
  {
    ret = lsm6dso_read_reg(ctx, LSM6DSO_PAGE_SEL, (uint8_t *) &page_sel, 1);
  }

  if (ret == 0)
  {
    page_sel.page_sel = ((uint8_t)(addr_pointed >> 8) & 0x0FU);
    page_sel.not_used_01 = 1;
    ret = lsm6dso_write_reg(ctx, LSM6DSO_PAGE_SEL, (uint8_t *) &page_sel, 1);
  }

  if (ret == 0)
  {
    page_address.page_addr = (uint8_t)(addr_pointed & 0x00FFU);
    ret = lsm6dso_write_reg(ctx, LSM6DSO_PAGE_ADDRESS,
                            (uint8_t *)&page_address, 1);
  }

  if (ret == 0)
  {
    for (i = 0; ((i < len) && (ret == 0)); i++)
    {
      ret = lsm6dso_write_reg(ctx, LSM6DSO_PAGE_VALUE, &buf[i], 1);
      addr_pointed++;

      /* Check if page wrap */
      if (((addr_pointed % 0x0100U) == 0x00U) && (ret == 0))
      {
        ret = lsm6dso_read_reg(ctx, LSM6DSO_PAGE_SEL, (uint8_t *)&page_sel, 1);

        if (ret == 0)
        {
          page_sel.page_sel = ((uint8_t)(addr_pointed >> 8) & 0x0FU);
          page_sel.not_used_01 = 1;
          ret = lsm6dso_write_reg(ctx, LSM6DSO_PAGE_SEL,
                                  (uint8_t *)&page_sel, 1);
        }
      }
    }

    page_sel.page_sel = 0;
    page_sel.not_used_01 = 1;
    ret = lsm6dso_write_reg(ctx, LSM6DSO_PAGE_SEL, (uint8_t *) &page_sel, 1);
  }

  if (ret == 0)
  {
    ret = lsm6dso_read_reg(ctx, LSM6DSO_PAGE_RW, (uint8_t *) &page_rw, 1);
  }

  if (ret == 0)
  {
    page_rw.page_rw = 0x00; /* page_write disable */
    ret = lsm6dso_write_reg(ctx, LSM6DSO_PAGE_RW, (uint8_t *) &page_rw, 1);
  }

  if (ret == 0)
  {
    ret = lsm6dso_mem_bank_set(ctx, LSM6DSO_USER_BANK);
  }

  return ret;
}

/**
  * @brief  Read a line(byte) in a page.[get]
  *
  * @param  ctx      read / write interface definitions
  * @param  uint8_t address: page line address
  * @param  val      read value
  * @retval             interface status (MANDATORY: return 0 -> no Error)
  *
  */
int32_t lsm6dso_ln_pg_read_byte(stmdev_ctx_t *ctx, uint16_t address,
                                uint8_t *val)
{
  lsm6dso_page_rw_t page_rw;
  lsm6dso_page_sel_t page_sel;
  lsm6dso_page_address_t  page_address;
  int32_t ret;

  ret = lsm6dso_mem_bank_set(ctx, LSM6DSO_EMBEDDED_FUNC_BANK);

  if (ret == 0)
  {
    ret = lsm6dso_read_reg(ctx, LSM6DSO_PAGE_RW, (uint8_t *) &page_rw, 1);
  }

  if (ret == 0)
  {
    page_rw.page_rw = 0x01; /* page_read enable*/
    ret = lsm6dso_write_reg(ctx, LSM6DSO_PAGE_RW, (uint8_t *) &page_rw, 1);
  }

  if (ret == 0)
  {
    ret = lsm6dso_read_reg(ctx, LSM6DSO_PAGE_SEL, (uint8_t *) &page_sel, 1);
  }

  if (ret == 0)
  {
    page_sel.page_sel = ((uint8_t)(address >> 8) & 0x0FU);
    page_sel.not_used_01 = 1;
    ret = lsm6dso_write_reg(ctx, LSM6DSO_PAGE_SEL, (uint8_t *) &page_sel, 1);
  }

  if (ret == 0)
  {
    page_address.page_addr = (uint8_t)address & 0x00FFU;
    ret = lsm6dso_write_reg(ctx, LSM6DSO_PAGE_ADDRESS,
                            (uint8_t *)&page_address, 1);
  }

  if (ret == 0)
  {
    ret = lsm6dso_read_reg(ctx, LSM6DSO_PAGE_VALUE, val, 1);
  }

  if (ret == 0)
  {
    ret = lsm6dso_read_reg(ctx, LSM6DSO_PAGE_RW, (uint8_t *) &page_rw, 1);
  }

  if (ret == 0)
  {
    page_rw.page_rw = 0x00; /* page_read disable */
    ret = lsm6dso_write_reg(ctx, LSM6DSO_PAGE_RW, (uint8_t *) &page_rw, 1);
  }

  if (ret == 0)
  {
    ret = lsm6dso_mem_bank_set(ctx, LSM6DSO_USER_BANK);
  }

  return ret;
}

/**
  * @brief  Data-ready pulsed / letched mode.[set]
  *
  * @param  ctx      read / write interface definitions
  * @param  val      change the values of
  *                                     dataready_pulsed in
  *                                     reg COUNTER_BDR_REG1
  * @retval             interface status (MANDATORY: return 0 -> no Error)
  *
  */
int32_t lsm6dso_data_ready_mode_set(stmdev_ctx_t *ctx,
                                    lsm6dso_dataready_pulsed_t val)
{
  lsm6dso_counter_bdr_reg1_t reg;
  int32_t ret;

  ret = lsm6dso_read_reg(ctx, LSM6DSO_COUNTER_BDR_REG1, (uint8_t *)&reg, 1);

  if (ret == 0)
  {
    reg.dataready_pulsed = (uint8_t)val;
    ret = lsm6dso_write_reg(ctx, LSM6DSO_COUNTER_BDR_REG1,
                            (uint8_t *)&reg, 1);
  }

  return ret;
}

/**
  * @brief  Data-ready pulsed / letched mode.[get]
  *
  * @param  ctx      read / write interface definitions
  * @param  val      Get the values of
  *                                     dataready_pulsed in
  *                                     reg COUNTER_BDR_REG1
  * @retval             interface status (MANDATORY: return 0 -> no Error)
  *
  */
int32_t lsm6dso_data_ready_mode_get(stmdev_ctx_t *ctx,
                                    lsm6dso_dataready_pulsed_t *val)
{
  lsm6dso_counter_bdr_reg1_t reg;
  int32_t ret;

  ret = lsm6dso_read_reg(ctx, LSM6DSO_COUNTER_BDR_REG1, (uint8_t *)&reg, 1);

  switch (reg.dataready_pulsed)
  {
    case LSM6DSO_DRDY_LATCHED:
      *val = LSM6DSO_DRDY_LATCHED;
      break;

    case LSM6DSO_DRDY_PULSED:
      *val = LSM6DSO_DRDY_PULSED;
      break;

    default:
      *val = LSM6DSO_DRDY_LATCHED;
      break;
  }

  return ret;
}

/**
  * @brief  Device "Who am I".[get]
  *
  * @param  ctx      read / write interface definitions
  * @param  buff     buffer that stores data read
  * @retval             interface status (MANDATORY: return 0 -> no Error)
  *
  */
int32_t lsm6dso_device_id_get(stmdev_ctx_t *ctx, uint8_t *buff)
{
  int32_t ret;

  ret = lsm6dso_read_reg(ctx, LSM6DSO_WHO_AM_I, buff, 1);

  return ret;
}

/**
  * @brief  Software reset. Restore the default values
  *         in user registers[set]
  *
  * @param  ctx      read / write interface definitions
  * @param  val      change the values of sw_reset in reg CTRL3_C
  * @retval             interface status (MANDATORY: return 0 -> no Error)
  *
  */
int32_t lsm6dso_reset_set(stmdev_ctx_t *ctx, uint8_t val)
{
  lsm6dso_ctrl3_c_t reg;
  int32_t ret;

  ret = lsm6dso_read_reg(ctx, LSM6DSO_CTRL3_C, (uint8_t *)&reg, 1);

  if (ret == 0)
  {
    reg.sw_reset = val;
    ret = lsm6dso_write_reg(ctx, LSM6DSO_CTRL3_C, (uint8_t *)&reg, 1);
  }

  return ret;
}

/**
  * @brief  Software reset. Restore the default values in user registers.[get]
  *
  * @param  ctx      read / write interface definitions
  * @param  val      change the values of sw_reset in reg CTRL3_C
  * @retval             interface status (MANDATORY: return 0 -> no Error)
  *
  */
int32_t lsm6dso_reset_get(stmdev_ctx_t *ctx, uint8_t *val)
{
  lsm6dso_ctrl3_c_t reg;
  int32_t ret;

  ret = lsm6dso_read_reg(ctx, LSM6DSO_CTRL3_C, (uint8_t *)&reg, 1);
  *val = reg.sw_reset;

  return ret;
}

/**
  * @brief  Register address automatically incremented during a multiple byte
  *         access with a serial interface.[set]
  *
  * @param  ctx      read / write interface definitions
  * @param  val      change the values of if_inc in reg CTRL3_C
  * @retval             interface status (MANDATORY: return 0 -> no Error)
  *
  */
int32_t lsm6dso_auto_increment_set(stmdev_ctx_t *ctx, uint8_t val)
{
  lsm6dso_ctrl3_c_t reg;
  int32_t ret;

  ret = lsm6dso_read_reg(ctx, LSM6DSO_CTRL3_C, (uint8_t *)&reg, 1);

  if (ret == 0)
  {
    reg.if_inc = val;
    ret = lsm6dso_write_reg(ctx, LSM6DSO_CTRL3_C, (uint8_t *)&reg, 1);
  }

  return ret;
}

/**
  * @brief  Register address automatically incremented during a multiple byte
  *         access with a serial interface.[get]
  *
  * @param  ctx      read / write interface definitions
  * @param  val      change the values of if_inc in reg CTRL3_C
  * @retval             interface status (MANDATORY: return 0 -> no Error)
  *
  */
int32_t lsm6dso_auto_increment_get(stmdev_ctx_t *ctx, uint8_t *val)
{
  lsm6dso_ctrl3_c_t reg;
  int32_t ret;

  ret = lsm6dso_read_reg(ctx, LSM6DSO_CTRL3_C, (uint8_t *)&reg, 1);
  *val = reg.if_inc;

  return ret;
}

/**
  * @brief  Reboot memory content. Reload the calibration parameters.[set]
  *
  * @param  ctx      read / write interface definitions
  * @param  val      change the values of boot in reg CTRL3_C
  * @retval             interface status (MANDATORY: return 0 -> no Error)
  *
  */
int32_t lsm6dso_boot_set(stmdev_ctx_t *ctx, uint8_t val)
{
  lsm6dso_ctrl3_c_t reg;
  int32_t ret;

  ret = lsm6dso_read_reg(ctx, LSM6DSO_CTRL3_C, (uint8_t *)&reg, 1);

  if (ret == 0)
  {
    reg.boot = val;
    ret = lsm6dso_write_reg(ctx, LSM6DSO_CTRL3_C, (uint8_t *)&reg, 1);
  }

  return ret;
}

/**
  * @brief  Reboot memory content. Reload the calibration parameters.[get]
  *
  * @param  ctx      read / write interface definitions
  * @param  val      change the values of boot in reg CTRL3_C
  * @retval             interface status (MANDATORY: return 0 -> no Error)
  *
  */
int32_t lsm6dso_boot_get(stmdev_ctx_t *ctx, uint8_t *val)
{
  lsm6dso_ctrl3_c_t reg;
  int32_t ret;

  ret = lsm6dso_read_reg(ctx, LSM6DSO_CTRL3_C, (uint8_t *)&reg, 1);
  *val = reg.boot;

  return ret;
}

/**
  * @brief  Linear acceleration sensor self-test enable.[set]
  *
  * @param  ctx      read / write interface definitions
  * @param  val      change the values of st_xl in reg CTRL5_C
  * @retval             interface status (MANDATORY: return 0 -> no Error)
  *
  */
int32_t lsm6dso_xl_self_test_set(stmdev_ctx_t *ctx,
                                 lsm6dso_st_xl_t val)
{
  lsm6dso_ctrl5_c_t reg;
  int32_t ret;

  ret = lsm6dso_read_reg(ctx, LSM6DSO_CTRL5_C, (uint8_t *)&reg, 1);

  if (ret == 0)
  {
    reg.st_xl = (uint8_t)val;
    ret = lsm6dso_write_reg(ctx, LSM6DSO_CTRL5_C, (uint8_t *)&reg, 1);
  }

  return ret;
}

/**
  * @brief  Linear acceleration sensor self-test enable.[get]
  *
  * @param  ctx      read / write interface definitions
  * @param  val      Get the values of st_xl in reg CTRL5_C
  * @retval             interface status (MANDATORY: return 0 -> no Error)
  *
  */
int32_t lsm6dso_xl_self_test_get(stmdev_ctx_t *ctx,
                                 lsm6dso_st_xl_t *val)
{
  lsm6dso_ctrl5_c_t reg;
  int32_t ret;

  ret = lsm6dso_read_reg(ctx, LSM6DSO_CTRL5_C, (uint8_t *)&reg, 1);

  switch (reg.st_xl)
  {
    case LSM6DSO_XL_ST_DISABLE:
      *val = LSM6DSO_XL_ST_DISABLE;
      break;

    case LSM6DSO_XL_ST_POSITIVE:
      *val = LSM6DSO_XL_ST_POSITIVE;
      break;

    case LSM6DSO_XL_ST_NEGATIVE:
      *val = LSM6DSO_XL_ST_NEGATIVE;
      break;

    default:
      *val = LSM6DSO_XL_ST_DISABLE;
      break;
  }

  return ret;
}

/**
  * @brief  Angular rate sensor self-test enable.[set]
  *
  * @param  ctx      read / write interface definitions
  * @param  val      change the values of st_g in reg CTRL5_C
  * @retval             interface status (MANDATORY: return 0 -> no Error)
  *
  */
int32_t lsm6dso_gy_self_test_set(stmdev_ctx_t *ctx,
                                 lsm6dso_st_g_t val)
{
  lsm6dso_ctrl5_c_t reg;
  int32_t ret;

  ret = lsm6dso_read_reg(ctx, LSM6DSO_CTRL5_C, (uint8_t *)&reg, 1);

  if (ret == 0)
  {
    reg.st_g = (uint8_t)val;
    ret = lsm6dso_write_reg(ctx, LSM6DSO_CTRL5_C, (uint8_t *)&reg, 1);
  }

  return ret;
}

/**
  * @brief  Angular rate sensor self-test enable.[get]
  *
  * @param  ctx      read / write interface definitions
  * @param  val      Get the values of st_g in reg CTRL5_C
  * @retval             interface status (MANDATORY: return 0 -> no Error)
  *
  */
int32_t lsm6dso_gy_self_test_get(stmdev_ctx_t *ctx,
                                 lsm6dso_st_g_t *val)
{
  lsm6dso_ctrl5_c_t reg;
  int32_t ret;

  ret = lsm6dso_read_reg(ctx, LSM6DSO_CTRL5_C, (uint8_t *)&reg, 1);

  switch (reg.st_g)
  {
    case LSM6DSO_GY_ST_DISABLE:
      *val = LSM6DSO_GY_ST_DISABLE;
      break;

    case LSM6DSO_GY_ST_POSITIVE:
      *val = LSM6DSO_GY_ST_POSITIVE;
      break;

    case LSM6DSO_GY_ST_NEGATIVE:
      *val = LSM6DSO_GY_ST_NEGATIVE;
      break;

    default:
      *val = LSM6DSO_GY_ST_DISABLE;
      break;
  }

  return ret;
}

/**
  * @}
  *
  */

/**
  * @defgroup  LSM6DSO_filters
  * @brief     This section group all the functions concerning the
  *            filters configuration
  * @{
  *
  */

/**
  * @brief  Accelerometer output from LPF2 filtering stage selection.[set]
  *
  * @param  ctx      read / write interface definitions
  * @param  val      change the values of lpf2_xl_en in reg CTRL1_XL
  * @retval             interface status (MANDATORY: return 0 -> no Error)
  *
  */
int32_t lsm6dso_xl_filter_lp2_set(stmdev_ctx_t *ctx, uint8_t val)
{
  lsm6dso_ctrl1_xl_t reg;
  int32_t ret;

  ret = lsm6dso_read_reg(ctx, LSM6DSO_CTRL1_XL, (uint8_t *)&reg, 1);

  if (ret == 0)
  {
    reg.lpf2_xl_en = val;
    ret = lsm6dso_write_reg(ctx, LSM6DSO_CTRL1_XL, (uint8_t *)&reg, 1);
  }

  return ret;
}

/**
  * @brief  Accelerometer output from LPF2 filtering stage selection.[get]
  *
  * @param  ctx      read / write interface definitions
  * @param  val      change the values of lpf2_xl_en in reg CTRL1_XL
  * @retval             interface status (MANDATORY: return 0 -> no Error)
  *
  */
int32_t lsm6dso_xl_filter_lp2_get(stmdev_ctx_t *ctx, uint8_t *val)
{
  lsm6dso_ctrl1_xl_t reg;
  int32_t ret;

  ret = lsm6dso_read_reg(ctx, LSM6DSO_CTRL1_XL, (uint8_t *)&reg, 1);
  *val = reg.lpf2_xl_en;

  return ret;
}

/**
  * @brief  Enables gyroscope digital LPF1 if auxiliary SPI is disabled;
  *         the bandwidth can be selected through FTYPE [2:0]
  *         in CTRL6_C (15h).[set]
  *
  * @param  ctx      read / write interface definitions
  * @param  val      change the values of lpf1_sel_g in reg CTRL4_C
  * @retval             interface status (MANDATORY: return 0 -> no Error)
  *
  */
int32_t lsm6dso_gy_filter_lp1_set(stmdev_ctx_t *ctx, uint8_t val)
{
  lsm6dso_ctrl4_c_t reg;
  int32_t ret;

  ret = lsm6dso_read_reg(ctx, LSM6DSO_CTRL4_C, (uint8_t *)&reg, 1);

  if (ret == 0)
  {
    reg.lpf1_sel_g = val;
    ret = lsm6dso_write_reg(ctx, LSM6DSO_CTRL4_C, (uint8_t *)&reg, 1);
  }

  return ret;
}

/**
  * @brief  Enables gyroscope digital LPF1 if auxiliary SPI is disabled;
  *         the bandwidth can be selected through FTYPE [2:0]
  *         in CTRL6_C (15h).[get]
  *
  * @param  ctx      read / write interface definitions
  * @param  val      change the values of lpf1_sel_g in reg CTRL4_C
  * @retval             interface status (MANDATORY: return 0 -> no Error)
  *
  */
int32_t lsm6dso_gy_filter_lp1_get(stmdev_ctx_t *ctx, uint8_t *val)
{
  lsm6dso_ctrl4_c_t reg;
  int32_t ret;

  ret = lsm6dso_read_reg(ctx, LSM6DSO_CTRL4_C, (uint8_t *)&reg, 1);
  *val = reg.lpf1_sel_g;

  return ret;
}

/**
  * @brief  Mask DRDY on pin (both XL & Gyro) until filter settling ends
  *         (XL and Gyro independently masked).[set]
  *
  * @param  ctx      read / write interface definitions
  * @param  val      change the values of drdy_mask in reg CTRL4_C
  * @retval             interface status (MANDATORY: return 0 -> no Error)
  *
  */
int32_t lsm6dso_filter_settling_mask_set(stmdev_ctx_t *ctx,
                                         uint8_t val)
{
  lsm6dso_ctrl4_c_t reg;
  int32_t ret;

  ret = lsm6dso_read_reg(ctx, LSM6DSO_CTRL4_C, (uint8_t *)&reg, 1);

  if (ret == 0)
  {
    reg.drdy_mask = val;
    ret = lsm6dso_write_reg(ctx, LSM6DSO_CTRL4_C, (uint8_t *)&reg, 1);
  }

  return ret;
}

/**
  * @brief  Mask DRDY on pin (both XL & Gyro) until filter settling ends
  *         (XL and Gyro independently masked).[get]
  *
  * @param  ctx      read / write interface definitions
  * @param  val      change the values of drdy_mask in reg CTRL4_C
  * @retval             interface status (MANDATORY: return 0 -> no Error)
  *
  */
int32_t lsm6dso_filter_settling_mask_get(stmdev_ctx_t *ctx,
                                         uint8_t *val)
{
  lsm6dso_ctrl4_c_t reg;
  int32_t ret;

  ret = lsm6dso_read_reg(ctx, LSM6DSO_CTRL4_C, (uint8_t *)&reg, 1);
  *val = reg.drdy_mask;

  return ret;
}

/**
  * @brief  Gyroscope lp1 bandwidth.[set]
  *
  * @param  ctx      read / write interface definitions
  * @param  val      change the values of ftype in reg CTRL6_C
  * @retval             interface status (MANDATORY: return 0 -> no Error)
  *
  */
int32_t lsm6dso_gy_lp1_bandwidth_set(stmdev_ctx_t *ctx,
                                     lsm6dso_ftype_t val)
{
  lsm6dso_ctrl6_c_t reg;
  int32_t ret;

  ret = lsm6dso_read_reg(ctx, LSM6DSO_CTRL6_C, (uint8_t *)&reg, 1);

  if (ret == 0)
  {
    reg.ftype = (uint8_t)val;
    ret = lsm6dso_write_reg(ctx, LSM6DSO_CTRL6_C, (uint8_t *)&reg, 1);
  }

  return ret;
}

/**
  * @brief  Gyroscope lp1 bandwidth.[get]
  *
  * @param  ctx      read / write interface definitions
  * @param  val       Get the values of ftype in reg CTRL6_C
  * @retval             interface status (MANDATORY: return 0 -> no Error)
  *
  */
int32_t lsm6dso_gy_lp1_bandwidth_get(stmdev_ctx_t *ctx,
                                     lsm6dso_ftype_t *val)
{
  lsm6dso_ctrl6_c_t reg;
  int32_t ret;

  ret = lsm6dso_read_reg(ctx, LSM6DSO_CTRL6_C, (uint8_t *)&reg, 1);

  switch (reg.ftype)
  {
    case LSM6DSO_ULTRA_LIGHT:
      *val = LSM6DSO_ULTRA_LIGHT;
      break;

    case LSM6DSO_VERY_LIGHT:
      *val = LSM6DSO_VERY_LIGHT;
      break;

    case LSM6DSO_LIGHT:
      *val = LSM6DSO_LIGHT;
      break;

    case LSM6DSO_MEDIUM:
      *val = LSM6DSO_MEDIUM;
      break;

    case LSM6DSO_STRONG:
      *val = LSM6DSO_STRONG;
      break;

    case LSM6DSO_VERY_STRONG:
      *val = LSM6DSO_VERY_STRONG;
      break;

    case LSM6DSO_AGGRESSIVE:
      *val = LSM6DSO_AGGRESSIVE;
      break;

    case LSM6DSO_XTREME:
      *val = LSM6DSO_XTREME;
      break;

    default:
      *val = LSM6DSO_ULTRA_LIGHT;
      break;
  }

  return ret;
}

/**
  * @brief  Low pass filter 2 on 6D function selection.[set]
  *
  * @param  ctx      read / write interface definitions
  * @param  val      change the values of low_pass_on_6d in reg CTRL8_XL
  * @retval             interface status (MANDATORY: return 0 -> no Error)
  *
  */
int32_t lsm6dso_xl_lp2_on_6d_set(stmdev_ctx_t *ctx, uint8_t val)
{
  lsm6dso_ctrl8_xl_t reg;
  int32_t ret;

  ret = lsm6dso_read_reg(ctx, LSM6DSO_CTRL8_XL, (uint8_t *)&reg, 1);

  if (ret == 0)
  {
    reg.low_pass_on_6d = val;
    ret = lsm6dso_write_reg(ctx, LSM6DSO_CTRL8_XL, (uint8_t *)&reg, 1);
  }

  return ret;
}

/**
  * @brief  Low pass filter 2 on 6D function selection.[get]
  *
  * @param  ctx      read / write interface definitions
  * @param  val      change the values of low_pass_on_6d in reg CTRL8_XL
  * @retval             interface status (MANDATORY: return 0 -> no Error)
  *
  */
int32_t lsm6dso_xl_lp2_on_6d_get(stmdev_ctx_t *ctx, uint8_t *val)
{
  lsm6dso_ctrl8_xl_t reg;
  int32_t ret;

  ret = lsm6dso_read_reg(ctx, LSM6DSO_CTRL8_XL, (uint8_t *)&reg, 1);
  *val = reg.low_pass_on_6d;

  return ret;
}

/**
  * @brief  Accelerometer slope filter / high-pass filter selection
  *         on output.[set]
  *
  * @param  ctx      read / write interface definitions
  * @param  val      change the values of hp_slope_xl_en
  *                                   in reg CTRL8_XL
  * @retval             interface status (MANDATORY: return 0 -> no Error)
  *
  */
int32_t lsm6dso_xl_hp_path_on_out_set(stmdev_ctx_t *ctx,
                                      lsm6dso_hp_slope_xl_en_t val)
{
  lsm6dso_ctrl8_xl_t reg;
  int32_t ret;

  ret = lsm6dso_read_reg(ctx, LSM6DSO_CTRL8_XL, (uint8_t *)&reg, 1);

  if (ret == 0)
  {
    reg.hp_slope_xl_en = ((uint8_t)val & 0x10U) >> 4;
    reg.hp_ref_mode_xl = ((uint8_t)val & 0x20U) >> 5;
    reg.hpcf_xl = (uint8_t)val & 0x07U;
    ret = lsm6dso_write_reg(ctx, LSM6DSO_CTRL8_XL, (uint8_t *)&reg, 1);
  }

  return ret;
}

/**
  * @brief  Accelerometer slope filter / high-pass filter selection
  *         on output.[get]
  *
  * @param  ctx      read / write interface definitions
  * @param  val      Get the values of hp_slope_xl_en
  *                                   in reg CTRL8_XL
  * @retval             interface status (MANDATORY: return 0 -> no Error)
  *
  */
int32_t lsm6dso_xl_hp_path_on_out_get(stmdev_ctx_t *ctx,
                                      lsm6dso_hp_slope_xl_en_t *val)
{
  lsm6dso_ctrl8_xl_t reg;
  int32_t ret;

  ret = lsm6dso_read_reg(ctx, LSM6DSO_CTRL8_XL, (uint8_t *)&reg, 1);

  switch ((reg.hp_ref_mode_xl << 5) | (reg.hp_slope_xl_en << 4) |
          reg.hpcf_xl)
  {
    case LSM6DSO_HP_PATH_DISABLE_ON_OUT:
      *val = LSM6DSO_HP_PATH_DISABLE_ON_OUT;
      break;

    case LSM6DSO_SLOPE_ODR_DIV_4:
      *val = LSM6DSO_SLOPE_ODR_DIV_4;
      break;

    case LSM6DSO_HP_ODR_DIV_10:
      *val = LSM6DSO_HP_ODR_DIV_10;
      break;

    case LSM6DSO_HP_ODR_DIV_20:
      *val = LSM6DSO_HP_ODR_DIV_20;
      break;

    case LSM6DSO_HP_ODR_DIV_45:
      *val = LSM6DSO_HP_ODR_DIV_45;
      break;

    case LSM6DSO_HP_ODR_DIV_100:
      *val = LSM6DSO_HP_ODR_DIV_100;
      break;

    case LSM6DSO_HP_ODR_DIV_200:
      *val = LSM6DSO_HP_ODR_DIV_200;
      break;

    case LSM6DSO_HP_ODR_DIV_400:
      *val = LSM6DSO_HP_ODR_DIV_400;
      break;

    case LSM6DSO_HP_ODR_DIV_800:
      *val = LSM6DSO_HP_ODR_DIV_800;
      break;

    case LSM6DSO_HP_REF_MD_ODR_DIV_10:
      *val = LSM6DSO_HP_REF_MD_ODR_DIV_10;
      break;

    case LSM6DSO_HP_REF_MD_ODR_DIV_20:
      *val = LSM6DSO_HP_REF_MD_ODR_DIV_20;
      break;

    case LSM6DSO_HP_REF_MD_ODR_DIV_45:
      *val = LSM6DSO_HP_REF_MD_ODR_DIV_45;
      break;

    case LSM6DSO_HP_REF_MD_ODR_DIV_100:
      *val = LSM6DSO_HP_REF_MD_ODR_DIV_100;
      break;

    case LSM6DSO_HP_REF_MD_ODR_DIV_200:
      *val = LSM6DSO_HP_REF_MD_ODR_DIV_200;
      break;

    case LSM6DSO_HP_REF_MD_ODR_DIV_400:
      *val = LSM6DSO_HP_REF_MD_ODR_DIV_400;
      break;

    case LSM6DSO_HP_REF_MD_ODR_DIV_800:
      *val = LSM6DSO_HP_REF_MD_ODR_DIV_800;
      break;

    case LSM6DSO_LP_ODR_DIV_10:
      *val = LSM6DSO_LP_ODR_DIV_10;
      break;

    case LSM6DSO_LP_ODR_DIV_20:
      *val = LSM6DSO_LP_ODR_DIV_20;
      break;

    case LSM6DSO_LP_ODR_DIV_45:
      *val = LSM6DSO_LP_ODR_DIV_45;
      break;

    case LSM6DSO_LP_ODR_DIV_100:
      *val = LSM6DSO_LP_ODR_DIV_100;
      break;

    case LSM6DSO_LP_ODR_DIV_200:
      *val = LSM6DSO_LP_ODR_DIV_200;
      break;

    case LSM6DSO_LP_ODR_DIV_400:
      *val = LSM6DSO_LP_ODR_DIV_400;
      break;

    case LSM6DSO_LP_ODR_DIV_800:
      *val = LSM6DSO_LP_ODR_DIV_800;
      break;

    default:
      *val = LSM6DSO_HP_PATH_DISABLE_ON_OUT;
      break;
  }

  return ret;
}

/**
  * @brief  Enables accelerometer LPF2 and HPF fast-settling mode.
  *         The filter sets the second samples after writing this bit.
  *         Active only during device exit from power-down mode.[set]
  *
  * @param  ctx      read / write interface definitions
  * @param  val      change the values of fastsettl_mode_xl in
  *                  reg CTRL8_XL
  * @retval             interface status (MANDATORY: return 0 -> no Error)
  *
  */
int32_t lsm6dso_xl_fast_settling_set(stmdev_ctx_t *ctx, uint8_t val)
{
  lsm6dso_ctrl8_xl_t reg;
  int32_t ret;

  ret = lsm6dso_read_reg(ctx, LSM6DSO_CTRL8_XL, (uint8_t *)&reg, 1);

  if (ret == 0)
  {
    reg.fastsettl_mode_xl = val;
    ret = lsm6dso_write_reg(ctx, LSM6DSO_CTRL8_XL, (uint8_t *)&reg, 1);
  }

  return ret;
}

/**
  * @brief  Enables accelerometer LPF2 and HPF fast-settling mode.
  *         The filter sets the second samples after writing this bit.
  *         Active only during device exit from power-down mode.[get]
  *
  * @param  ctx      read / write interface definitions
  * @param  val      change the values of fastsettl_mode_xl in reg CTRL8_XL
  * @retval             interface status (MANDATORY: return 0 -> no Error)
  *
  */
int32_t lsm6dso_xl_fast_settling_get(stmdev_ctx_t *ctx, uint8_t *val)
{
  lsm6dso_ctrl8_xl_t reg;
  int32_t ret;

  ret = lsm6dso_read_reg(ctx, LSM6DSO_CTRL8_XL, (uint8_t *)&reg, 1);
  *val = reg.fastsettl_mode_xl;

  return ret;
}

/**
  * @brief  HPF or SLOPE filter selection on wake-up and Activity/Inactivity
  *         functions.[set]
  *
  * @param  ctx      read / write interface definitions
  * @param  val      change the values of slope_fds in reg TAP_CFG0
  * @retval             interface status (MANDATORY: return 0 -> no Error)
  *
  */
int32_t lsm6dso_xl_hp_path_internal_set(stmdev_ctx_t *ctx,
                                        lsm6dso_slope_fds_t val)
{
  lsm6dso_tap_cfg0_t reg;
  int32_t ret;

  ret = lsm6dso_read_reg(ctx, LSM6DSO_TAP_CFG0, (uint8_t *)&reg, 1);

  if (ret == 0)
  {
    reg.slope_fds = (uint8_t)val;
    ret = lsm6dso_write_reg(ctx, LSM6DSO_TAP_CFG0, (uint8_t *)&reg, 1);
  }

  return ret;
}

/**
  * @brief  HPF or SLOPE filter selection on wake-up and Activity/Inactivity
  *         functions.[get]
  *
  * @param  ctx      read / write interface definitions
  * @param  val      Get the values of slope_fds in reg TAP_CFG0
  * @retval             interface status (MANDATORY: return 0 -> no Error)
  *
  */
int32_t lsm6dso_xl_hp_path_internal_get(stmdev_ctx_t *ctx,
                                        lsm6dso_slope_fds_t *val)
{
  lsm6dso_tap_cfg0_t reg;
  int32_t ret;

  ret = lsm6dso_read_reg(ctx, LSM6DSO_TAP_CFG0, (uint8_t *)&reg, 1);

  switch (reg.slope_fds)
  {
    case LSM6DSO_USE_SLOPE:
      *val = LSM6DSO_USE_SLOPE;
      break;

    case LSM6DSO_USE_HPF:
      *val = LSM6DSO_USE_HPF;
      break;

    default:
      *val = LSM6DSO_USE_SLOPE;
      break;
  }

  return ret;
}

/**
  * @brief  Enables gyroscope digital high-pass filter. The filter is
  *         enabled only if the gyro is in HP mode.[set]
  *
  * @param  ctx      read / write interface definitions
  * @param  val      Get the values of hp_en_g and hp_en_g
  *                            in reg CTRL7_G
  * @retval             interface status (MANDATORY: return 0 -> no Error)
  *
  */
int32_t lsm6dso_gy_hp_path_internal_set(stmdev_ctx_t *ctx,
                                        lsm6dso_hpm_g_t val)
{
  lsm6dso_ctrl7_g_t reg;
  int32_t ret;

  ret = lsm6dso_read_reg(ctx, LSM6DSO_CTRL7_G, (uint8_t *)&reg, 1);

  if (ret == 0)
  {
    reg.hp_en_g = ((uint8_t)val & 0x80U) >> 7;
    reg.hpm_g = (uint8_t)val & 0x03U;
    ret = lsm6dso_write_reg(ctx, LSM6DSO_CTRL7_G, (uint8_t *)&reg, 1);
  }

  return ret;
}

/**
  * @brief  Enables gyroscope digital high-pass filter. The filter is
  *         enabled only if the gyro is in HP mode.[get]
  *
  * @param  ctx      read / write interface definitions
  * @param  val      Get the values of hp_en_g and hp_en_g
  *                            in reg CTRL7_G
  * @retval             interface status (MANDATORY: return 0 -> no Error)
  *
  */
int32_t lsm6dso_gy_hp_path_internal_get(stmdev_ctx_t *ctx,
                                        lsm6dso_hpm_g_t *val)
{
  lsm6dso_ctrl7_g_t reg;
  int32_t ret;

  ret = lsm6dso_read_reg(ctx, LSM6DSO_CTRL7_G, (uint8_t *)&reg, 1);

  switch ((reg.hp_en_g << 7) + reg.hpm_g)
  {
    case LSM6DSO_HP_FILTER_NONE:
      *val = LSM6DSO_HP_FILTER_NONE;
      break;

    case LSM6DSO_HP_FILTER_16mHz:
      *val = LSM6DSO_HP_FILTER_16mHz;
      break;

    case LSM6DSO_HP_FILTER_65mHz:
      *val = LSM6DSO_HP_FILTER_65mHz;
      break;

    case LSM6DSO_HP_FILTER_260mHz:
      *val = LSM6DSO_HP_FILTER_260mHz;
      break;

    case LSM6DSO_HP_FILTER_1Hz04:
      *val = LSM6DSO_HP_FILTER_1Hz04;
      break;

    default:
      *val = LSM6DSO_HP_FILTER_NONE;
      break;
  }

  return ret;
}

/**
  * @}
  *
  */

/**
  * @defgroup  LSM6DSO_ Auxiliary_interface
  * @brief     This section groups all the functions concerning
  *            auxiliary interface.
  * @{
  *
  */

/**
  * @brief  aOn auxiliary interface connect/disconnect SDO and OCS
  *         internal pull-up.[set]
  *
  * @param  ctx      read / write interface definitions
  * @param  val      change the values of ois_pu_dis in
  *                               reg PIN_CTRL
  * @retval             interface status (MANDATORY: return 0 -> no Error)
  *
  */
int32_t lsm6dso_aux_sdo_ocs_mode_set(stmdev_ctx_t *ctx,
                                     lsm6dso_ois_pu_dis_t val)
{
  lsm6dso_pin_ctrl_t reg;
  int32_t ret;

  ret = lsm6dso_read_reg(ctx, LSM6DSO_PIN_CTRL, (uint8_t *)&reg, 1);

  if (ret == 0)
  {
    reg.ois_pu_dis = (uint8_t)val;
    ret = lsm6dso_write_reg(ctx, LSM6DSO_PIN_CTRL, (uint8_t *)&reg, 1);
  }

  return ret;
}

/**
  * @brief  On auxiliary interface connect/disconnect SDO and OCS
  *         internal pull-up.[get]
  *
  * @param  ctx      read / write interface definitions
  * @param  val      Get the values of ois_pu_dis in reg PIN_CTRL
  * @retval             interface status (MANDATORY: return 0 -> no Error)
  *
  */
int32_t lsm6dso_aux_sdo_ocs_mode_get(stmdev_ctx_t *ctx,
                                     lsm6dso_ois_pu_dis_t *val)
{
  lsm6dso_pin_ctrl_t reg;
  int32_t ret;

  ret = lsm6dso_read_reg(ctx, LSM6DSO_PIN_CTRL, (uint8_t *)&reg, 1);

  switch (reg.ois_pu_dis)
  {
    case LSM6DSO_AUX_PULL_UP_DISC:
      *val = LSM6DSO_AUX_PULL_UP_DISC;
      break;

    case LSM6DSO_AUX_PULL_UP_CONNECT:
      *val = LSM6DSO_AUX_PULL_UP_CONNECT;
      break;

    default:
      *val = LSM6DSO_AUX_PULL_UP_DISC;
      break;
  }

  return ret;
}

/**
  * @brief  OIS chain on aux interface power on mode.[set]
  *
  * @param  ctx      read / write interface definitions
  * @param  val      change the values of ois_on in reg CTRL7_G
  * @retval             interface status (MANDATORY: return 0 -> no Error)
  *
  */
int32_t lsm6dso_aux_pw_on_ctrl_set(stmdev_ctx_t *ctx,
                                   lsm6dso_ois_on_t val)
{
  lsm6dso_ctrl7_g_t reg;
  int32_t ret;

  ret = lsm6dso_read_reg(ctx, LSM6DSO_CTRL7_G, (uint8_t *)&reg, 1);

  if (ret == 0)
  {
    reg.ois_on_en = (uint8_t)val & 0x01U;
    reg.ois_on = (uint8_t)val & 0x01U;
    ret = lsm6dso_write_reg(ctx, LSM6DSO_CTRL7_G, (uint8_t *)&reg, 1);
  }

  return ret;
}

/**
  * @brief  aux_pw_on_ctrl: [get]  OIS chain on aux interface power on mode
  *
  * @param  ctx      read / write interface definitions
  * @param  val      Get the values of ois_on in reg CTRL7_G
  * @retval             interface status (MANDATORY: return 0 -> no Error)
  *
  */
int32_t lsm6dso_aux_pw_on_ctrl_get(stmdev_ctx_t *ctx,
                                   lsm6dso_ois_on_t *val)
{
  lsm6dso_ctrl7_g_t reg;
  int32_t ret;

  ret = lsm6dso_read_reg(ctx, LSM6DSO_CTRL7_G, (uint8_t *)&reg, 1);

  switch (reg.ois_on)
  {
    case LSM6DSO_AUX_ON:
      *val = LSM6DSO_AUX_ON;
      break;

    case LSM6DSO_AUX_ON_BY_AUX_INTERFACE:
      *val = LSM6DSO_AUX_ON_BY_AUX_INTERFACE;
      break;

    default:
      *val = LSM6DSO_AUX_ON;
      break;
  }

  return ret;
}

/**
  * @brief  Accelerometer full-scale management between UI chain and
  *         OIS chain. When XL UI is on, the full scale is the same
  *         between UI/OIS and is chosen by the UI CTRL registers;
  *         when XL UI is in PD, the OIS can choose the FS.
  *         Full scales are independent between the UI/OIS chain
  *         but both bound to 8 g.[set]
  *
  * @param  ctx      read / write interface definitions
  * @param  val      change the values of xl_fs_mode in
  *                               reg CTRL8_XL
  * @retval             interface status (MANDATORY: return 0 -> no Error)
  *
  */
int32_t lsm6dso_aux_xl_fs_mode_set(stmdev_ctx_t *ctx,
                                   lsm6dso_xl_fs_mode_t val)
{
  lsm6dso_ctrl8_xl_t reg;
  int32_t ret;

  ret = lsm6dso_read_reg(ctx, LSM6DSO_CTRL8_XL, (uint8_t *)&reg, 1);

  if (ret == 0)
  {
    reg.xl_fs_mode = (uint8_t)val;
    ret = lsm6dso_write_reg(ctx, LSM6DSO_CTRL8_XL, (uint8_t *)&reg, 1);
  }

  return ret;
}

/**
  * @brief  Accelerometer full-scale management between UI chain and
  *         OIS chain. When XL UI is on, the full scale is the same
  *         between UI/OIS and is chosen by the UI CTRL registers;
  *         when XL UI is in PD, the OIS can choose the FS.
  *         Full scales are independent between the UI/OIS chain
  *         but both bound to 8 g.[get]
  *
  * @param  ctx      read / write interface definitions
  * @param  val      Get the values of xl_fs_mode in reg CTRL8_XL
  * @retval             interface status (MANDATORY: return 0 -> no Error)
  *
  */
int32_t lsm6dso_aux_xl_fs_mode_get(stmdev_ctx_t *ctx,
                                   lsm6dso_xl_fs_mode_t *val)
{
  lsm6dso_ctrl8_xl_t reg;
  int32_t ret;

  ret = lsm6dso_read_reg(ctx, LSM6DSO_CTRL8_XL, (uint8_t *)&reg, 1);

  switch (reg.xl_fs_mode)
  {
    case LSM6DSO_USE_SAME_XL_FS:
      *val = LSM6DSO_USE_SAME_XL_FS;
      break;

    case LSM6DSO_USE_DIFFERENT_XL_FS:
      *val = LSM6DSO_USE_DIFFERENT_XL_FS;
      break;

    default:
      *val = LSM6DSO_USE_SAME_XL_FS;
      break;
  }

  return ret;
}

/**
  * @brief  The STATUS_SPIAux register is read by the auxiliary SPI.[get]
  *
  * @param  ctx      read / write interface definitions
  * @param  lsm6dso_status_spiaux_t: registers STATUS_SPIAUX
  * @retval             interface status (MANDATORY: return 0 -> no Error)
  *
  */
int32_t lsm6dso_aux_status_reg_get(stmdev_ctx_t *ctx,
                                   lsm6dso_status_spiaux_t *val)
{
  int32_t ret;

  ret = lsm6dso_read_reg(ctx, LSM6DSO_STATUS_SPIAUX, (uint8_t *) val, 1);

  return ret;
}

/**
  * @brief  aux_xl_flag_data_ready: [get]  AUX accelerometer data available
  *
  * @param  ctx      read / write interface definitions
  * @param  val      change the values of xlda in reg STATUS_SPIAUX
  * @retval             interface status (MANDATORY: return 0 -> no Error)
  *
  */
int32_t lsm6dso_aux_xl_flag_data_ready_get(stmdev_ctx_t *ctx,
                                           uint8_t *val)
{
  lsm6dso_status_spiaux_t reg;
  int32_t ret;

  ret = lsm6dso_read_reg(ctx, LSM6DSO_STATUS_SPIAUX, (uint8_t *)&reg, 1);
  *val = reg.xlda;

  return ret;
}

/**
  * @brief  aux_gy_flag_data_ready: [get]  AUX gyroscope data available.
  *
  * @param  ctx      read / write interface definitions
  * @param  val      change the values of gda in reg STATUS_SPIAUX
  * @retval             interface status (MANDATORY: return 0 -> no Error)
  *
  */
int32_t lsm6dso_aux_gy_flag_data_ready_get(stmdev_ctx_t *ctx,
                                           uint8_t *val)
{
  lsm6dso_status_spiaux_t reg;
  int32_t ret;

  ret = lsm6dso_read_reg(ctx, LSM6DSO_STATUS_SPIAUX, (uint8_t *)&reg, 1);
  *val = reg.gda;

  return ret;
}

/**
  * @brief  High when the gyroscope output is in the settling phase.[get]
  *
  * @param  ctx      read / write interface definitions
  * @param  val      change the values of gyro_settling in reg STATUS_SPIAUX
  * @retval             interface status (MANDATORY: return 0 -> no Error)
  *
  */
int32_t lsm6dso_aux_gy_flag_settling_get(stmdev_ctx_t *ctx,
                                         uint8_t *val)
{
  lsm6dso_status_spiaux_t reg;
  int32_t ret;

  ret = lsm6dso_read_reg(ctx, LSM6DSO_STATUS_SPIAUX, (uint8_t *)&reg, 1);
  *val = reg.gyro_settling;

  return ret;
}

/**
  * @brief  Selects accelerometer self-test. Effective only if XL OIS
  *         chain is enabled.[set]
  *
  * @param  ctx      read / write interface definitions
  * @param  val      change the values of st_xl_ois in reg INT_OIS
  * @retval             interface status (MANDATORY: return 0 -> no Error)
  *
  */
int32_t lsm6dso_aux_xl_self_test_set(stmdev_ctx_t *ctx,
                                     lsm6dso_st_xl_ois_t val)
{
  lsm6dso_int_ois_t reg;
  int32_t ret;

  ret = lsm6dso_read_reg(ctx, LSM6DSO_INT_OIS, (uint8_t *)&reg, 1);

  if (ret == 0)
  {
    reg.st_xl_ois = (uint8_t)val;
    ret = lsm6dso_write_reg(ctx, LSM6DSO_INT_OIS, (uint8_t *)&reg, 1);
  }

  return ret;
}

/**
  * @brief  Selects accelerometer self-test. Effective only if XL OIS
  *         chain is enabled.[get]
  *
  * @param  ctx      read / write interface definitions
  * @param  val      Get the values of st_xl_ois in reg INT_OIS
  * @retval             interface status (MANDATORY: return 0 -> no Error)
  *
  */
int32_t lsm6dso_aux_xl_self_test_get(stmdev_ctx_t *ctx,
                                     lsm6dso_st_xl_ois_t *val)
{
  lsm6dso_int_ois_t reg;
  int32_t ret;

  ret = lsm6dso_read_reg(ctx, LSM6DSO_INT_OIS, (uint8_t *)&reg, 1);

  switch (reg.st_xl_ois)
  {
    case LSM6DSO_AUX_XL_DISABLE:
      *val = LSM6DSO_AUX_XL_DISABLE;
      break;

    case LSM6DSO_AUX_XL_POS:
      *val = LSM6DSO_AUX_XL_POS;
      break;

    case LSM6DSO_AUX_XL_NEG:
      *val = LSM6DSO_AUX_XL_NEG;
      break;

    default:
      *val = LSM6DSO_AUX_XL_DISABLE;
      break;
  }

  return ret;
}

/**
  * @brief  Indicates polarity of DEN signal on OIS chain.[set]
  *
  * @param  ctx      read / write interface definitions
  * @param  val      change the values of den_lh_ois in
  *                  reg INT_OIS
  * @retval             interface status (MANDATORY: return 0 -> no Error)
  *
  */
int32_t lsm6dso_aux_den_polarity_set(stmdev_ctx_t *ctx,
                                     lsm6dso_den_lh_ois_t val)
{
  lsm6dso_int_ois_t reg;
  int32_t ret;

  ret = lsm6dso_read_reg(ctx, LSM6DSO_INT_OIS, (uint8_t *)&reg, 1);

  if (ret == 0)
  {
    reg.den_lh_ois = (uint8_t)val;
    ret = lsm6dso_write_reg(ctx, LSM6DSO_INT_OIS, (uint8_t *)&reg, 1);
  }

  return ret;
}

/**
  * @brief  Indicates polarity of DEN signal on OIS chain.[get]
  *
  * @param  ctx      read / write interface definitions
  * @param  val      Get the values of den_lh_ois in reg INT_OIS
  * @retval             interface status (MANDATORY: return 0 -> no Error)
  *
  */
int32_t lsm6dso_aux_den_polarity_get(stmdev_ctx_t *ctx,
                                     lsm6dso_den_lh_ois_t *val)
{
  lsm6dso_int_ois_t reg;
  int32_t ret;

  ret = lsm6dso_read_reg(ctx, LSM6DSO_INT_OIS, (uint8_t *)&reg, 1);

  switch (reg.den_lh_ois)
  {
    case LSM6DSO_AUX_DEN_ACTIVE_LOW:
      *val = LSM6DSO_AUX_DEN_ACTIVE_LOW;
      break;

    case LSM6DSO_AUX_DEN_ACTIVE_HIGH:
      *val = LSM6DSO_AUX_DEN_ACTIVE_HIGH;
      break;

    default:
      *val = LSM6DSO_AUX_DEN_ACTIVE_LOW;
      break;
  }

  return ret;
}

/**
  * @brief  Configure DEN mode on the OIS chain.[set]
  *
  * @param  ctx      read / write interface definitions
  * @param  val      change the values of lvl2_ois in reg INT_OIS
  * @retval             interface status (MANDATORY: return 0 -> no Error)
  *
  */
int32_t lsm6dso_aux_den_mode_set(stmdev_ctx_t *ctx,
                                 lsm6dso_lvl2_ois_t val)
{
  lsm6dso_ctrl1_ois_t ctrl1_ois;
  lsm6dso_int_ois_t int_ois;
  int32_t ret;

  ret = lsm6dso_read_reg(ctx, LSM6DSO_INT_OIS, (uint8_t *) &int_ois, 1);

  if (ret == 0)
  {
    int_ois.lvl2_ois = (uint8_t)val & 0x01U;
    ret = lsm6dso_write_reg(ctx, LSM6DSO_INT_OIS, (uint8_t *) &int_ois, 1);
  }

  if (ret == 0)
  {
    ret = lsm6dso_read_reg(ctx, LSM6DSO_CTRL1_OIS, (uint8_t *) &ctrl1_ois, 1);
  }

  if (ret == 0)
  {
    ctrl1_ois.lvl1_ois = ((uint8_t)val & 0x02U) >> 1;
    ret = lsm6dso_write_reg(ctx, LSM6DSO_CTRL1_OIS,
                            (uint8_t *) &ctrl1_ois, 1);
  }

  return ret;
}

/**
  * @brief  Configure DEN mode on the OIS chain.[get]
  *
  * @param  ctx      read / write interface definitions
  * @param  val      Get the values of lvl2_ois in reg INT_OIS
  * @retval             interface status (MANDATORY: return 0 -> no Error)
  *
  */
int32_t lsm6dso_aux_den_mode_get(stmdev_ctx_t *ctx,
                                 lsm6dso_lvl2_ois_t *val)
{
  lsm6dso_ctrl1_ois_t ctrl1_ois;
  lsm6dso_int_ois_t int_ois;
  int32_t ret;

  ret = lsm6dso_read_reg(ctx, LSM6DSO_INT_OIS, (uint8_t *) &int_ois, 1);

  if (ret == 0)
  {
    ret = lsm6dso_read_reg(ctx, LSM6DSO_CTRL1_OIS, (uint8_t *) &ctrl1_ois, 1);

    switch ((ctrl1_ois.lvl1_ois << 1) + int_ois.lvl2_ois)
    {
      case LSM6DSO_AUX_DEN_DISABLE:
        *val = LSM6DSO_AUX_DEN_DISABLE;
        break;

      case LSM6DSO_AUX_DEN_LEVEL_LATCH:
        *val = LSM6DSO_AUX_DEN_LEVEL_LATCH;
        break;

      case LSM6DSO_AUX_DEN_LEVEL_TRIG:
        *val = LSM6DSO_AUX_DEN_LEVEL_TRIG;
        break;

      default:
        *val = LSM6DSO_AUX_DEN_DISABLE;
        break;
    }
  }

  return ret;
}

/**
  * @brief  Enables/Disable OIS chain DRDY on INT2 pin.
  *         This setting has priority over all other INT2 settings.[set]
  *
  * @param  ctx      read / write interface definitions
  * @param  val      change the values of int2_drdy_ois in reg INT_OIS
  * @retval             interface status (MANDATORY: return 0 -> no Error)
  *
  */
int32_t lsm6dso_aux_drdy_on_int2_set(stmdev_ctx_t *ctx, uint8_t val)
{
  lsm6dso_int_ois_t reg;
  int32_t ret;

  ret = lsm6dso_read_reg(ctx, LSM6DSO_INT_OIS, (uint8_t *)&reg, 1);

  if (ret == 0)
  {
    reg.int2_drdy_ois = val;
    ret = lsm6dso_write_reg(ctx, LSM6DSO_INT_OIS, (uint8_t *)&reg, 1);
  }

  return ret;
}

/**
  * @brief  Enables/Disable OIS chain DRDY on INT2 pin.
  *         This setting has priority over all other INT2 settings.[get]
  *
  * @param  ctx      read / write interface definitions
  * @param  val      change the values of int2_drdy_ois in reg INT_OIS
  * @retval             interface status (MANDATORY: return 0 -> no Error)
  *
  */
int32_t lsm6dso_aux_drdy_on_int2_get(stmdev_ctx_t *ctx, uint8_t *val)
{
  lsm6dso_int_ois_t reg;
  int32_t ret;

  ret = lsm6dso_read_reg(ctx, LSM6DSO_INT_OIS, (uint8_t *)&reg, 1);
  *val = reg.int2_drdy_ois;

  return ret;
}

/**
  * @brief  Enables OIS chain data processing for gyro in Mode 3 and Mode 4
  *         (mode4_en = 1) and accelerometer data in and Mode 4 (mode4_en = 1).
  *         When the OIS chain is enabled, the OIS outputs are available
  *         through the SPI2 in registers OUTX_L_G (22h) through
  *         OUTZ_H_G (27h) and STATUS_REG (1Eh) / STATUS_SPIAux, and
  *         LPF1 is dedicated to this chain.[set]
  *
  * @param  ctx      read / write interface definitions
  * @param  val      change the values of ois_en_spi2 in
  *                                reg CTRL1_OIS
  * @retval             interface status (MANDATORY: return 0 -> no Error)
  *
  */
int32_t lsm6dso_aux_mode_set(stmdev_ctx_t *ctx,
                             lsm6dso_ois_en_spi2_t val)
{
  lsm6dso_ctrl1_ois_t reg;
  int32_t ret;

  ret = lsm6dso_read_reg(ctx, LSM6DSO_CTRL1_OIS, (uint8_t *)&reg, 1);

  if (ret == 0)
  {
    reg.ois_en_spi2 = (uint8_t)val & 0x01U;
    reg.mode4_en = ((uint8_t)val & 0x02U) >> 1;
    ret = lsm6dso_write_reg(ctx, LSM6DSO_CTRL1_OIS, (uint8_t *)&reg, 1);
  }

  return ret;
}

/**
  * @brief  Enables OIS chain data processing for gyro in Mode 3 and Mode 4
  *         (mode4_en = 1) and accelerometer data in and Mode 4 (mode4_en = 1).
  *         When the OIS chain is enabled, the OIS outputs are available
  *         through the SPI2 in registers OUTX_L_G (22h) through
  *         OUTZ_H_G (27h) and STATUS_REG (1Eh) / STATUS_SPIAux, and
  *         LPF1 is dedicated to this chain.[get]
  *
  * @param  ctx      read / write interface definitions
  * @param  val      Get the values of ois_en_spi2 in
  *                                reg CTRL1_OIS
  * @retval             interface status (MANDATORY: return 0 -> no Error)
  *
  */
int32_t lsm6dso_aux_mode_get(stmdev_ctx_t *ctx,
                             lsm6dso_ois_en_spi2_t *val)
{
  lsm6dso_ctrl1_ois_t reg;
  int32_t ret;

  ret = lsm6dso_read_reg(ctx, LSM6DSO_CTRL1_OIS, (uint8_t *)&reg, 1);

  switch ((reg.mode4_en << 1) | reg.ois_en_spi2)
  {
    case LSM6DSO_AUX_DISABLE:
      *val = LSM6DSO_AUX_DISABLE;
      break;

    case LSM6DSO_MODE_3_GY:
      *val = LSM6DSO_MODE_3_GY;
      break;

    case LSM6DSO_MODE_4_GY_XL:
      *val = LSM6DSO_MODE_4_GY_XL;
      break;

    default:
      *val = LSM6DSO_AUX_DISABLE;
      break;
  }

  return ret;
}

/**
  * @brief  Selects gyroscope OIS chain full-scale.[set]
  *
  * @param  ctx      read / write interface definitions
  * @param  val      change the values of fs_g_ois in reg CTRL1_OIS
  * @retval             interface status (MANDATORY: return 0 -> no Error)
  *
  */
int32_t lsm6dso_aux_gy_full_scale_set(stmdev_ctx_t *ctx,
                                      lsm6dso_fs_g_ois_t val)
{
  lsm6dso_ctrl1_ois_t reg;
  int32_t ret;

  ret = lsm6dso_read_reg(ctx, LSM6DSO_CTRL1_OIS, (uint8_t *)&reg, 1);

  if (ret == 0)
  {
    reg.fs_g_ois = (uint8_t)val;
    ret = lsm6dso_write_reg(ctx, LSM6DSO_CTRL1_OIS, (uint8_t *)&reg, 1);
  }

  return ret;
}

/**
  * @brief  Selects gyroscope OIS chain full-scale.[get]
  *
  * @param  ctx      read / write interface definitions
  * @param  val      Get the values of fs_g_ois in reg CTRL1_OIS
  * @retval             interface status (MANDATORY: return 0 -> no Error)
  *
  */
int32_t lsm6dso_aux_gy_full_scale_get(stmdev_ctx_t *ctx,
                                      lsm6dso_fs_g_ois_t *val)
{
  lsm6dso_ctrl1_ois_t reg;
  int32_t ret;

  ret = lsm6dso_read_reg(ctx, LSM6DSO_CTRL1_OIS, (uint8_t *)&reg, 1);

  switch (reg.fs_g_ois)
  {
    case LSM6DSO_250dps_AUX:
      *val = LSM6DSO_250dps_AUX;
      break;

    case LSM6DSO_125dps_AUX:
      *val = LSM6DSO_125dps_AUX;
      break;

    case LSM6DSO_500dps_AUX:
      *val = LSM6DSO_500dps_AUX;
      break;

    case LSM6DSO_1000dps_AUX:
      *val = LSM6DSO_1000dps_AUX;
      break;

    case LSM6DSO_2000dps_AUX:
      *val = LSM6DSO_2000dps_AUX;
      break;

    default:
      *val = LSM6DSO_250dps_AUX;
      break;
  }

  return ret;
}

/**
  * @brief  SPI2 3- or 4-wire interface.[set]
  *
  * @param  ctx      read / write interface definitions
  * @param  val      change the values of sim_ois in reg CTRL1_OIS
  * @retval             interface status (MANDATORY: return 0 -> no Error)
  *
  */
int32_t lsm6dso_aux_spi_mode_set(stmdev_ctx_t *ctx,
                                 lsm6dso_sim_ois_t val)
{
  lsm6dso_ctrl1_ois_t reg;
  int32_t ret;

  ret = lsm6dso_read_reg(ctx, LSM6DSO_CTRL1_OIS, (uint8_t *)&reg, 1);

  if (ret == 0)
  {
    reg.sim_ois = (uint8_t)val;
    ret = lsm6dso_write_reg(ctx, LSM6DSO_CTRL1_OIS, (uint8_t *)&reg, 1);
  }

  return ret;
}

/**
  * @brief  SPI2 3- or 4-wire interface.[get]
  *
  * @param  ctx      read / write interface definitions
  * @param  val      Get the values of sim_ois in reg CTRL1_OIS
  * @retval             interface status (MANDATORY: return 0 -> no Error)
  *
  */
int32_t lsm6dso_aux_spi_mode_get(stmdev_ctx_t *ctx,
                                 lsm6dso_sim_ois_t *val)
{
  lsm6dso_ctrl1_ois_t reg;
  int32_t ret;

  ret = lsm6dso_read_reg(ctx, LSM6DSO_CTRL1_OIS, (uint8_t *)&reg, 1);

  switch (reg.sim_ois)
  {
    case LSM6DSO_AUX_SPI_4_WIRE:
      *val = LSM6DSO_AUX_SPI_4_WIRE;
      break;

    case LSM6DSO_AUX_SPI_3_WIRE:
      *val = LSM6DSO_AUX_SPI_3_WIRE;
      break;

    default:
      *val = LSM6DSO_AUX_SPI_4_WIRE;
      break;
  }

  return ret;
}

/**
  * @brief  Selects gyroscope digital LPF1 filter bandwidth.[set]
  *
  * @param  ctx      read / write interface definitions
  * @param  val      change the values of ftype_ois in
  *                              reg CTRL2_OIS
  * @retval             interface status (MANDATORY: return 0 -> no Error)
  *
  */
int32_t lsm6dso_aux_gy_lp1_bandwidth_set(stmdev_ctx_t *ctx,
                                         lsm6dso_ftype_ois_t val)
{
  lsm6dso_ctrl2_ois_t reg;
  int32_t ret;

  ret = lsm6dso_read_reg(ctx, LSM6DSO_CTRL2_OIS, (uint8_t *)&reg, 1);

  if (ret == 0)
  {
    reg.ftype_ois = (uint8_t)val;
    ret = lsm6dso_write_reg(ctx, LSM6DSO_CTRL2_OIS, (uint8_t *)&reg, 1);
  }

  return ret;
}

/**
  * @brief  Selects gyroscope digital LPF1 filter bandwidth.[get]
  *
  * @param  ctx      read / write interface definitions
  * @param  val      Get the values of ftype_ois in reg CTRL2_OIS
  * @retval             interface status (MANDATORY: return 0 -> no Error)
  *
  */
int32_t lsm6dso_aux_gy_lp1_bandwidth_get(stmdev_ctx_t *ctx,
                                         lsm6dso_ftype_ois_t *val)
{
  lsm6dso_ctrl2_ois_t reg;
  int32_t ret;

  ret = lsm6dso_read_reg(ctx, LSM6DSO_CTRL2_OIS, (uint8_t *)&reg, 1);

  switch (reg.ftype_ois)
  {
    case LSM6DSO_351Hz39:
      *val = LSM6DSO_351Hz39;
      break;

    case LSM6DSO_236Hz63:
      *val = LSM6DSO_236Hz63;
      break;

    case LSM6DSO_172Hz70:
      *val = LSM6DSO_172Hz70;
      break;

    case LSM6DSO_937Hz91:
      *val = LSM6DSO_937Hz91;
      break;

    default:
      *val = LSM6DSO_351Hz39;
      break;
  }

  return ret;
}

/**
  * @brief  Selects gyroscope OIS chain digital high-pass filter cutoff.[set]
  *
  * @param  ctx      read / write interface definitions
  * @param  val      change the values of hpm_ois in reg CTRL2_OIS
  * @retval             interface status (MANDATORY: return 0 -> no Error)
  *
  */
int32_t lsm6dso_aux_gy_hp_bandwidth_set(stmdev_ctx_t *ctx,
                                        lsm6dso_hpm_ois_t val)
{
  lsm6dso_ctrl2_ois_t reg;
  int32_t ret;

  ret = lsm6dso_read_reg(ctx, LSM6DSO_CTRL2_OIS, (uint8_t *)&reg, 1);

  if (ret == 0)
  {
    reg.hpm_ois = (uint8_t)val & 0x03U;
    reg.hp_en_ois = ((uint8_t)val & 0x10U) >> 4;
    ret = lsm6dso_write_reg(ctx, LSM6DSO_CTRL2_OIS, (uint8_t *)&reg, 1);
  }

  return ret;
}

/**
  * @brief  Selects gyroscope OIS chain digital high-pass filter cutoff.[get]
  *
  * @param  ctx      read / write interface definitions
  * @param  val      Get the values of hpm_ois in reg CTRL2_OIS
  * @retval             interface status (MANDATORY: return 0 -> no Error)
  *
  */
int32_t lsm6dso_aux_gy_hp_bandwidth_get(stmdev_ctx_t *ctx,
                                        lsm6dso_hpm_ois_t *val)
{
  lsm6dso_ctrl2_ois_t reg;
  int32_t ret;

  ret = lsm6dso_read_reg(ctx, LSM6DSO_CTRL2_OIS, (uint8_t *)&reg, 1);

  switch ((reg.hp_en_ois << 4) | reg.hpm_ois)
  {
    case LSM6DSO_AUX_HP_DISABLE:
      *val = LSM6DSO_AUX_HP_DISABLE;
      break;

    case LSM6DSO_AUX_HP_Hz016:
      *val = LSM6DSO_AUX_HP_Hz016;
      break;

    case LSM6DSO_AUX_HP_Hz065:
      *val = LSM6DSO_AUX_HP_Hz065;
      break;

    case LSM6DSO_AUX_HP_Hz260:
      *val = LSM6DSO_AUX_HP_Hz260;
      break;

    case LSM6DSO_AUX_HP_1Hz040:
      *val = LSM6DSO_AUX_HP_1Hz040;
      break;

    default:
      *val = LSM6DSO_AUX_HP_DISABLE;
      break;
  }

  return ret;
}

/**
  * @brief  Enable / Disables OIS chain clamp.
  *         Enable: All OIS chain outputs = 8000h
  *         during self-test; Disable: OIS chain self-test
  *         outputs dependent from the aux gyro full
  *         scale selected.[set]
  *
  * @param  ctx      read / write interface definitions
  * @param  val      change the values of st_ois_clampdis in
  *                                    reg CTRL3_OIS
  * @retval             interface status (MANDATORY: return 0 -> no Error)
  *
  */
int32_t lsm6dso_aux_gy_clamp_set(stmdev_ctx_t *ctx,
                                 lsm6dso_st_ois_clampdis_t val)
{
  lsm6dso_ctrl3_ois_t reg;
  int32_t ret;

  ret = lsm6dso_read_reg(ctx, LSM6DSO_CTRL3_OIS, (uint8_t *)&reg, 1);

  if (ret == 0)
  {
    reg.st_ois_clampdis = (uint8_t)val;
    ret = lsm6dso_write_reg(ctx, LSM6DSO_CTRL3_OIS, (uint8_t *)&reg, 1);
  }

  return ret;
}

/**
  * @brief  Enable / Disables OIS chain clamp.
  *         Enable: All OIS chain outputs = 8000h
  *         during self-test; Disable: OIS chain self-test
  *         outputs dependent from the aux gyro full
  *         scale selected.[set]
  *
  * @param  ctx      read / write interface definitions
  * @param  val      Get the values of st_ois_clampdis in
  *                                    reg CTRL3_OIS
  * @retval             interface status (MANDATORY: return 0 -> no Error)
  *
  */
int32_t lsm6dso_aux_gy_clamp_get(stmdev_ctx_t *ctx,
                                 lsm6dso_st_ois_clampdis_t *val)
{
  lsm6dso_ctrl3_ois_t reg;
  int32_t ret;

  ret = lsm6dso_read_reg(ctx, LSM6DSO_CTRL3_OIS, (uint8_t *)&reg, 1);

  switch (reg.st_ois_clampdis)
  {
    case LSM6DSO_ENABLE_CLAMP:
      *val = LSM6DSO_ENABLE_CLAMP;
      break;

    case LSM6DSO_DISABLE_CLAMP:
      *val = LSM6DSO_DISABLE_CLAMP;
      break;

    default:
      *val = LSM6DSO_ENABLE_CLAMP;
      break;
  }

  return ret;
}

/**
  * @brief  Selects gyroscope OIS chain self-test.[set]
  *
  * @param  ctx      read / write interface definitions
  * @param  val      change the values of st_ois in reg CTRL3_OIS
  * @retval             interface status (MANDATORY: return 0 -> no Error)
  *
  */
int32_t lsm6dso_aux_gy_self_test_set(stmdev_ctx_t *ctx,
                                     lsm6dso_st_ois_t val)
{
  lsm6dso_ctrl3_ois_t reg;
  int32_t ret;

  ret = lsm6dso_read_reg(ctx, LSM6DSO_CTRL3_OIS, (uint8_t *)&reg, 1);

  if (ret == 0)
  {
    reg.st_ois = (uint8_t)val;
    ret = lsm6dso_write_reg(ctx, LSM6DSO_CTRL3_OIS, (uint8_t *)&reg, 1);
  }

  return ret;
}

/**
  * @brief  Selects gyroscope OIS chain self-test.[get]
  *
  * @param  ctx      read / write interface definitions
  * @param  val      Get the values of st_ois in reg CTRL3_OIS
  * @retval             interface status (MANDATORY: return 0 -> no Error)
  *
  */
int32_t lsm6dso_aux_gy_self_test_get(stmdev_ctx_t *ctx,
                                     lsm6dso_st_ois_t *val)
{
  lsm6dso_ctrl3_ois_t reg;
  int32_t ret;

  ret = lsm6dso_read_reg(ctx, LSM6DSO_CTRL3_OIS, (uint8_t *)&reg, 1);

  switch (reg.st_ois)
  {
    case LSM6DSO_AUX_GY_DISABLE:
      *val = LSM6DSO_AUX_GY_DISABLE;
      break;

    case LSM6DSO_AUX_GY_POS:
      *val = LSM6DSO_AUX_GY_POS;
      break;

    case LSM6DSO_AUX_GY_NEG:
      *val = LSM6DSO_AUX_GY_NEG;
      break;

    default:
      *val = LSM6DSO_AUX_GY_DISABLE;
      break;
  }

  return ret;
}

/**
  * @brief  Selects accelerometer OIS channel bandwidth.[set]
  *
  * @param  ctx      read / write interface definitions
  * @param  val      change the values of
  *                                       filter_xl_conf_ois in reg CTRL3_OIS
  * @retval             interface status (MANDATORY: return 0 -> no Error)
  *
  */
int32_t lsm6dso_aux_xl_bandwidth_set(stmdev_ctx_t *ctx,
                                     lsm6dso_filter_xl_conf_ois_t val)
{
  lsm6dso_ctrl3_ois_t reg;
  int32_t ret;

  ret = lsm6dso_read_reg(ctx, LSM6DSO_CTRL3_OIS, (uint8_t *)&reg, 1);

  if (ret == 0)
  {
    reg.filter_xl_conf_ois = (uint8_t)val;
    ret = lsm6dso_write_reg(ctx, LSM6DSO_CTRL3_OIS, (uint8_t *)&reg, 1);
  }

  return ret;
}

/**
  * @brief  Selects accelerometer OIS channel bandwidth.[get]
  *
  * @param  ctx      read / write interface definitions
  * @param  val      Get the values of
  *                                       filter_xl_conf_ois in reg CTRL3_OIS
  * @retval             interface status (MANDATORY: return 0 -> no Error)
  *
  */
int32_t lsm6dso_aux_xl_bandwidth_get(stmdev_ctx_t *ctx,
                                     lsm6dso_filter_xl_conf_ois_t *val)
{
  lsm6dso_ctrl3_ois_t reg;
  int32_t ret;

  ret = lsm6dso_read_reg(ctx, LSM6DSO_CTRL3_OIS, (uint8_t *)&reg, 1);

  switch (reg.filter_xl_conf_ois)
  {
    case LSM6DSO_289Hz:
      *val = LSM6DSO_289Hz;
      break;

    case LSM6DSO_258Hz:
      *val = LSM6DSO_258Hz;
      break;

    case LSM6DSO_120Hz:
      *val = LSM6DSO_120Hz;
      break;

    case LSM6DSO_65Hz2:
      *val = LSM6DSO_65Hz2;
      break;

    case LSM6DSO_33Hz2:
      *val = LSM6DSO_33Hz2;
      break;

    case LSM6DSO_16Hz6:
      *val = LSM6DSO_16Hz6;
      break;

    case LSM6DSO_8Hz30:
      *val = LSM6DSO_8Hz30;
      break;

    case LSM6DSO_4Hz15:
      *val = LSM6DSO_4Hz15;
      break;

    default:
      *val = LSM6DSO_289Hz;
      break;
  }

  return ret;
}

/**
  * @brief  Selects accelerometer OIS channel full-scale.[set]
  *
  * @param  ctx      read / write interface definitions
  * @param  val      change the values of fs_xl_ois in
  *                              reg CTRL3_OIS
  * @retval             interface status (MANDATORY: return 0 -> no Error)
  *
  */
int32_t lsm6dso_aux_xl_full_scale_set(stmdev_ctx_t *ctx,
                                      lsm6dso_fs_xl_ois_t val)
{
  lsm6dso_ctrl3_ois_t reg;
  int32_t ret;

  ret = lsm6dso_read_reg(ctx, LSM6DSO_CTRL3_OIS, (uint8_t *)&reg, 1);

  if (ret == 0)
  {
    reg.fs_xl_ois = (uint8_t)val;
    ret = lsm6dso_write_reg(ctx, LSM6DSO_CTRL3_OIS, (uint8_t *)&reg, 1);
  }

  return ret;
}

/**
  * @brief  Selects accelerometer OIS channel full-scale.[get]
  *
  * @param  ctx      read / write interface definitions
  * @param  val      Get the values of fs_xl_ois in reg CTRL3_OIS
  * @retval             interface status (MANDATORY: return 0 -> no Error)
  *
  */
int32_t lsm6dso_aux_xl_full_scale_get(stmdev_ctx_t *ctx,
                                      lsm6dso_fs_xl_ois_t *val)
{
  lsm6dso_ctrl3_ois_t reg;
  int32_t ret;

  ret = lsm6dso_read_reg(ctx, LSM6DSO_CTRL3_OIS, (uint8_t *)&reg, 1);

  switch (reg.fs_xl_ois)
  {
    case LSM6DSO_AUX_2g:
      *val = LSM6DSO_AUX_2g;
      break;

    case LSM6DSO_AUX_16g:
      *val = LSM6DSO_AUX_16g;
      break;

    case LSM6DSO_AUX_4g:
      *val = LSM6DSO_AUX_4g;
      break;

    case LSM6DSO_AUX_8g:
      *val = LSM6DSO_AUX_8g;
      break;

    default:
      *val = LSM6DSO_AUX_2g;
      break;
  }

  return ret;
}

/**
  * @}
  *
  */

/**
  * @defgroup  LSM6DSO_ main_serial_interface
  * @brief     This section groups all the functions concerning main
  *            serial interface management (not auxiliary)
  * @{
  *
  */

/**
  * @brief  Connect/Disconnect SDO/SA0 internal pull-up.[set]
  *
  * @param  ctx      read / write interface definitions
  * @param  val      change the values of sdo_pu_en in
  *                              reg PIN_CTRL
  * @retval             interface status (MANDATORY: return 0 -> no Error)
  *
  */
int32_t lsm6dso_sdo_sa0_mode_set(stmdev_ctx_t *ctx,
                                 lsm6dso_sdo_pu_en_t val)
{
  lsm6dso_pin_ctrl_t reg;
  int32_t ret;

  ret = lsm6dso_read_reg(ctx, LSM6DSO_PIN_CTRL, (uint8_t *)&reg, 1);

  if (ret == 0)
  {
    reg.sdo_pu_en = (uint8_t)val;
    ret = lsm6dso_write_reg(ctx, LSM6DSO_PIN_CTRL, (uint8_t *)&reg, 1);
  }

  return ret;
}

/**
  * @brief  Connect/Disconnect SDO/SA0 internal pull-up.[get]
  *
  * @param  ctx      read / write interface definitions
  * @param  val      Get the values of sdo_pu_en in reg PIN_CTRL
  * @retval             interface status (MANDATORY: return 0 -> no Error)
  *
  */
int32_t lsm6dso_sdo_sa0_mode_get(stmdev_ctx_t *ctx,
                                 lsm6dso_sdo_pu_en_t *val)
{
  lsm6dso_pin_ctrl_t reg;
  int32_t ret;

  ret = lsm6dso_read_reg(ctx, LSM6DSO_PIN_CTRL, (uint8_t *)&reg, 1);

  switch (reg.sdo_pu_en)
  {
    case LSM6DSO_PULL_UP_DISC:
      *val = LSM6DSO_PULL_UP_DISC;
      break;

    case LSM6DSO_PULL_UP_CONNECT:
      *val = LSM6DSO_PULL_UP_CONNECT;
      break;

    default:
      *val = LSM6DSO_PULL_UP_DISC;
      break;
  }

  return ret;
}

/**
  * @brief  SPI Serial Interface Mode selection.[set]
  *
  * @param  ctx      read / write interface definitions
  * @param  val      change the values of sim in reg CTRL3_C
  * @retval             interface status (MANDATORY: return 0 -> no Error)
  *
  */
int32_t lsm6dso_spi_mode_set(stmdev_ctx_t *ctx, lsm6dso_sim_t val)
{
  lsm6dso_ctrl3_c_t reg;
  int32_t ret;

  ret = lsm6dso_read_reg(ctx, LSM6DSO_CTRL3_C, (uint8_t *)&reg, 1);

  if (ret == 0)
  {
    reg.sim = (uint8_t)val;
    ret = lsm6dso_write_reg(ctx, LSM6DSO_CTRL3_C, (uint8_t *)&reg, 1);
  }

  return ret;
}

/**
  * @brief  SPI Serial Interface Mode selection.[get]
  *
  * @param  ctx      read / write interface definitions
  * @param  val      Get the values of sim in reg CTRL3_C
  * @retval             interface status (MANDATORY: return 0 -> no Error)
  *
  */
int32_t lsm6dso_spi_mode_get(stmdev_ctx_t *ctx, lsm6dso_sim_t *val)
{
  lsm6dso_ctrl3_c_t reg;
  int32_t ret;

  ret = lsm6dso_read_reg(ctx, LSM6DSO_CTRL3_C, (uint8_t *)&reg, 1);

  switch (reg.sim)
  {
    case LSM6DSO_SPI_4_WIRE:
      *val = LSM6DSO_SPI_4_WIRE;
      break;

    case LSM6DSO_SPI_3_WIRE:
      *val = LSM6DSO_SPI_3_WIRE;
      break;

    default:
      *val = LSM6DSO_SPI_4_WIRE;
      break;
  }

  return ret;
}

/**
  * @brief  Disable / Enable I2C interface.[set]
  *
  * @param  ctx      read / write interface definitions
  * @param  val      change the values of i2c_disable in
  *                                reg CTRL4_C
  * @retval             interface status (MANDATORY: return 0 -> no Error)
  *
  */
int32_t lsm6dso_i2c_interface_set(stmdev_ctx_t *ctx,
                                  lsm6dso_i2c_disable_t val)
{
  lsm6dso_ctrl4_c_t reg;
  int32_t ret;

  ret = lsm6dso_read_reg(ctx, LSM6DSO_CTRL4_C, (uint8_t *)&reg, 1);

  if (ret == 0)
  {
    reg.i2c_disable = (uint8_t)val;
    ret = lsm6dso_write_reg(ctx, LSM6DSO_CTRL4_C, (uint8_t *)&reg, 1);
  }

  return ret;
}

/**
  * @brief  Disable / Enable I2C interface.[get]
  *
  * @param  ctx      read / write interface definitions
  * @param  val      Get the values of i2c_disable in
  *                                reg CTRL4_C
  * @retval             interface status (MANDATORY: return 0 -> no Error)
  *
  */
int32_t lsm6dso_i2c_interface_get(stmdev_ctx_t *ctx,
                                  lsm6dso_i2c_disable_t *val)
{
  lsm6dso_ctrl4_c_t reg;
  int32_t ret;

  ret = lsm6dso_read_reg(ctx, LSM6DSO_CTRL4_C, (uint8_t *)&reg, 1);

  switch (reg.i2c_disable)
  {
    case LSM6DSO_I2C_ENABLE:
      *val = LSM6DSO_I2C_ENABLE;
      break;

    case LSM6DSO_I2C_DISABLE:
      *val = LSM6DSO_I2C_DISABLE;
      break;

    default:
      *val = LSM6DSO_I2C_ENABLE;
      break;
  }

  return ret;
}

/**
  * @brief  I3C Enable/Disable communication protocol[.set]
  *
  * @param  ctx      read / write interface definitions
  * @param  val      change the values of i3c_disable
  *                                    in reg CTRL9_XL
  * @retval             interface status (MANDATORY: return 0 -> no Error)
  *
  */
int32_t lsm6dso_i3c_disable_set(stmdev_ctx_t *ctx,
                                lsm6dso_i3c_disable_t val)
{
  lsm6dso_i3c_bus_avb_t i3c_bus_avb;
  lsm6dso_ctrl9_xl_t ctrl9_xl;
  int32_t ret;

  ret = lsm6dso_read_reg(ctx, LSM6DSO_CTRL9_XL, (uint8_t *)&ctrl9_xl, 1);

  if (ret == 0)
  {
    ctrl9_xl.i3c_disable = ((uint8_t)val & 0x80U) >> 7;
    ret = lsm6dso_write_reg(ctx, LSM6DSO_CTRL9_XL, (uint8_t *)&ctrl9_xl, 1);
  }

  if (ret == 0)
  {
    ret = lsm6dso_read_reg(ctx, LSM6DSO_I3C_BUS_AVB,
                           (uint8_t *)&i3c_bus_avb, 1);
  }

  if (ret == 0)
  {
    i3c_bus_avb.i3c_bus_avb_sel = (uint8_t)val & 0x03U;
    ret = lsm6dso_write_reg(ctx, LSM6DSO_I3C_BUS_AVB,
                            (uint8_t *)&i3c_bus_avb, 1);
  }

  return ret;
}

/**
  * @brief  I3C Enable/Disable communication protocol.[get]
  *
  * @param  ctx      read / write interface definitions
  * @param  val      change the values of i3c_disable in
  *                                reg CTRL9_XL
  * @retval             interface status (MANDATORY: return 0 -> no Error)
  *
  */
int32_t lsm6dso_i3c_disable_get(stmdev_ctx_t *ctx,
                                lsm6dso_i3c_disable_t *val)
{
  lsm6dso_ctrl9_xl_t ctrl9_xl;
  lsm6dso_i3c_bus_avb_t i3c_bus_avb;
  int32_t ret;

  ret = lsm6dso_read_reg(ctx, LSM6DSO_CTRL9_XL, (uint8_t *)&ctrl9_xl, 1);

  if (ret == 0)
  {
    ret = lsm6dso_read_reg(ctx, LSM6DSO_I3C_BUS_AVB,
                           (uint8_t *)&i3c_bus_avb, 1);

    switch ((ctrl9_xl.i3c_disable << 7) | i3c_bus_avb.i3c_bus_avb_sel)
    {
      case LSM6DSO_I3C_DISABLE:
        *val = LSM6DSO_I3C_DISABLE;
        break;

      case LSM6DSO_I3C_ENABLE_T_50us:
        *val = LSM6DSO_I3C_ENABLE_T_50us;
        break;

      case LSM6DSO_I3C_ENABLE_T_2us:
        *val = LSM6DSO_I3C_ENABLE_T_2us;
        break;

      case LSM6DSO_I3C_ENABLE_T_1ms:
        *val = LSM6DSO_I3C_ENABLE_T_1ms;
        break;

      case LSM6DSO_I3C_ENABLE_T_25ms:
        *val = LSM6DSO_I3C_ENABLE_T_25ms;
        break;

      default:
        *val = LSM6DSO_I3C_DISABLE;
        break;
    }
  }

  return ret;
}

/**
  * @}
  *
  */

/**
  * @defgroup  LSM6DSO_interrupt_pins
  * @brief     This section groups all the functions that manage interrupt pins
  * @{
  *
  */

/**
  * @brief  Connect/Disconnect INT1 internal pull-down.[set]
  *
  * @param  ctx      read / write interface definitions
  * @param  val      change the values of pd_dis_int1 in reg I3C_BUS_AVB
  * @retval             interface status (MANDATORY: return 0 -> no Error)
  *
  */
int32_t lsm6dso_int1_mode_set(stmdev_ctx_t *ctx,
                              lsm6dso_int1_pd_en_t val)
{
  lsm6dso_i3c_bus_avb_t reg;
  int32_t ret;

  ret = lsm6dso_read_reg(ctx, LSM6DSO_I3C_BUS_AVB, (uint8_t *)&reg, 1);

  if (ret == 0)
  {
    reg.pd_dis_int1 = (uint8_t)val;
    ret = lsm6dso_write_reg(ctx, LSM6DSO_I3C_BUS_AVB, (uint8_t *)&reg, 1);
  }

  return ret;
}

/**
  * @brief  Connect/Disconnect INT1 internal pull-down.[get]
  *
  * @param  ctx      read / write interface definitions
  * @param  val      Get the values of pd_dis_int1 in reg I3C_BUS_AVB
  * @retval             interface status (MANDATORY: return 0 -> no Error)
  *
  */
int32_t lsm6dso_int1_mode_get(stmdev_ctx_t *ctx,
                              lsm6dso_int1_pd_en_t *val)
{
  lsm6dso_i3c_bus_avb_t reg;
  int32_t ret;

  ret = lsm6dso_read_reg(ctx, LSM6DSO_I3C_BUS_AVB, (uint8_t *)&reg, 1);

  switch (reg.pd_dis_int1)
  {
    case LSM6DSO_PULL_DOWN_DISC:
      *val = LSM6DSO_PULL_DOWN_DISC;
      break;

    case LSM6DSO_PULL_DOWN_CONNECT:
      *val = LSM6DSO_PULL_DOWN_CONNECT;
      break;

    default:
      *val = LSM6DSO_PULL_DOWN_DISC;
      break;
  }

  return ret;
}

/**
  * @brief  Push-pull/open drain selection on interrupt pads.[set]
  *
  * @param  ctx      read / write interface definitions
  * @param  val      change the values of pp_od in reg CTRL3_C
  * @retval             interface status (MANDATORY: return 0 -> no Error)
  *
  */
int32_t lsm6dso_pin_mode_set(stmdev_ctx_t *ctx, lsm6dso_pp_od_t val)
{
  lsm6dso_ctrl3_c_t reg;
  int32_t ret;

  ret = lsm6dso_read_reg(ctx, LSM6DSO_CTRL3_C, (uint8_t *)&reg, 1);

  if (ret == 0)
  {
    reg.pp_od = (uint8_t)val;
    ret = lsm6dso_write_reg(ctx, LSM6DSO_CTRL3_C, (uint8_t *)&reg, 1);
  }

  return ret;
}

/**
  * @brief  Push-pull/open drain selection on interrupt pads.[get]
  *
  * @param  ctx      read / write interface definitions
  * @param  val      Get the values of pp_od in reg CTRL3_C
  * @retval             interface status (MANDATORY: return 0 -> no Error)
  *
  */
int32_t lsm6dso_pin_mode_get(stmdev_ctx_t *ctx, lsm6dso_pp_od_t *val)
{
  lsm6dso_ctrl3_c_t reg;
  int32_t ret;

  ret = lsm6dso_read_reg(ctx, LSM6DSO_CTRL3_C, (uint8_t *)&reg, 1);

  switch (reg.pp_od)
  {
    case LSM6DSO_PUSH_PULL:
      *val = LSM6DSO_PUSH_PULL;
      break;

    case LSM6DSO_OPEN_DRAIN:
      *val = LSM6DSO_OPEN_DRAIN;
      break;

    default:
      *val = LSM6DSO_PUSH_PULL;
      break;
  }

  return ret;
}

/**
  * @brief  Interrupt active-high/low.[set]
  *
  * @param  ctx      read / write interface definitions
  * @param  val      change the values of h_lactive in reg CTRL3_C
  * @retval             interface status (MANDATORY: return 0 -> no Error)
  *
  */
int32_t lsm6dso_pin_polarity_set(stmdev_ctx_t *ctx,
                                 lsm6dso_h_lactive_t val)
{
  lsm6dso_ctrl3_c_t reg;
  int32_t ret;

  ret = lsm6dso_read_reg(ctx, LSM6DSO_CTRL3_C, (uint8_t *)&reg, 1);

  if (ret == 0)
  {
    reg.h_lactive = (uint8_t)val;
    ret = lsm6dso_write_reg(ctx, LSM6DSO_CTRL3_C, (uint8_t *)&reg, 1);
  }

  return ret;
}

/**
  * @brief  Interrupt active-high/low.[get]
  *
  * @param  ctx      read / write interface definitions
  * @param  val      Get the values of h_lactive in reg CTRL3_C
  * @retval             interface status (MANDATORY: return 0 -> no Error)
  *
  */
int32_t lsm6dso_pin_polarity_get(stmdev_ctx_t *ctx,
                                 lsm6dso_h_lactive_t *val)
{
  lsm6dso_ctrl3_c_t reg;
  int32_t ret;

  ret = lsm6dso_read_reg(ctx, LSM6DSO_CTRL3_C, (uint8_t *)&reg, 1);

  switch (reg.h_lactive)
  {
    case LSM6DSO_ACTIVE_HIGH:
      *val = LSM6DSO_ACTIVE_HIGH;
      break;

    case LSM6DSO_ACTIVE_LOW:
      *val = LSM6DSO_ACTIVE_LOW;
      break;

    default:
      *val = LSM6DSO_ACTIVE_HIGH;
      break;
  }

  return ret;
}

/**
  * @brief  All interrupt signals become available on INT1 pin.[set]
  *
  * @param  ctx      read / write interface definitions
  * @param  val      change the values of int2_on_int1 in reg CTRL4_C
  * @retval             interface status (MANDATORY: return 0 -> no Error)
  *
  */
int32_t lsm6dso_all_on_int1_set(stmdev_ctx_t *ctx, uint8_t val)
{
  lsm6dso_ctrl4_c_t reg;
  int32_t ret;

  ret = lsm6dso_read_reg(ctx, LSM6DSO_CTRL4_C, (uint8_t *)&reg, 1);

  if (ret == 0)
  {
    reg.int2_on_int1 = val;
    ret = lsm6dso_write_reg(ctx, LSM6DSO_CTRL4_C, (uint8_t *)&reg, 1);
  }

  return ret;
}

/**
  * @brief  All interrupt signals become available on INT1 pin.[get]
  *
  * @param  ctx      read / write interface definitions
  * @param  val      change the values of int2_on_int1 in reg CTRL4_C
  * @retval             interface status (MANDATORY: return 0 -> no Error)
  *
  */
int32_t lsm6dso_all_on_int1_get(stmdev_ctx_t *ctx, uint8_t *val)
{
  lsm6dso_ctrl4_c_t reg;
  int32_t ret;

  ret = lsm6dso_read_reg(ctx, LSM6DSO_CTRL4_C, (uint8_t *)&reg, 1);
  *val = reg.int2_on_int1;

  return ret;
}

/**
  * @brief  Interrupt notification mode.[set]
  *
  * @param  ctx      read / write interface definitions
  * @param  val      change the values of lir in reg TAP_CFG0
  * @retval             interface status (MANDATORY: return 0 -> no Error)
  *
  */
int32_t lsm6dso_int_notification_set(stmdev_ctx_t *ctx,
                                     lsm6dso_lir_t val)
{
  lsm6dso_tap_cfg0_t tap_cfg0;
  lsm6dso_page_rw_t page_rw;
  int32_t ret;

  ret = lsm6dso_read_reg(ctx, LSM6DSO_TAP_CFG0, (uint8_t *) &tap_cfg0, 1);

  if (ret == 0)
  {
    tap_cfg0.lir = (uint8_t)val & 0x01U;
    tap_cfg0.int_clr_on_read = (uint8_t)val & 0x01U;
    ret = lsm6dso_write_reg(ctx, LSM6DSO_TAP_CFG0, (uint8_t *) &tap_cfg0, 1);
  }

  if (ret == 0)
  {
    ret = lsm6dso_mem_bank_set(ctx, LSM6DSO_EMBEDDED_FUNC_BANK);
  }

  if (ret == 0)
  {
    ret = lsm6dso_read_reg(ctx, LSM6DSO_PAGE_RW, (uint8_t *) &page_rw, 1);
  }

  if (ret == 0)
  {
    page_rw.emb_func_lir = ((uint8_t)val & 0x02U) >> 1;
    ret = lsm6dso_write_reg(ctx, LSM6DSO_PAGE_RW, (uint8_t *) &page_rw, 1);
  }

  if (ret == 0)
  {
    ret = lsm6dso_mem_bank_set(ctx, LSM6DSO_USER_BANK);
  }

  return ret;
}

/**
  * @brief  Interrupt notification mode.[get]
  *
  * @param  ctx      read / write interface definitions
  * @param  val      Get the values of lir in reg TAP_CFG0
  * @retval             interface status (MANDATORY: return 0 -> no Error)
  *
  */
int32_t lsm6dso_int_notification_get(stmdev_ctx_t *ctx,
                                     lsm6dso_lir_t *val)
{
  lsm6dso_tap_cfg0_t tap_cfg0;
  lsm6dso_page_rw_t page_rw;
  int32_t ret;

  ret = lsm6dso_read_reg(ctx, LSM6DSO_TAP_CFG0, (uint8_t *) &tap_cfg0, 1);

  if (ret == 0)
  {
    ret = lsm6dso_mem_bank_set(ctx, LSM6DSO_EMBEDDED_FUNC_BANK);
  }

  if (ret == 0)
  {
    ret = lsm6dso_read_reg(ctx, LSM6DSO_PAGE_RW, (uint8_t *) &page_rw, 1);
  }

  if (ret == 0)
  {
    ret = lsm6dso_mem_bank_set(ctx, LSM6DSO_USER_BANK);
  }

  if (ret == 0)
  {
    switch ((page_rw.emb_func_lir << 1) | tap_cfg0.lir)
    {
      case LSM6DSO_ALL_INT_PULSED:
        *val = LSM6DSO_ALL_INT_PULSED;
        break;

      case LSM6DSO_BASE_LATCHED_EMB_PULSED:
        *val = LSM6DSO_BASE_LATCHED_EMB_PULSED;
        break;

      case LSM6DSO_BASE_PULSED_EMB_LATCHED:
        *val = LSM6DSO_BASE_PULSED_EMB_LATCHED;
        break;

      case LSM6DSO_ALL_INT_LATCHED:
        *val = LSM6DSO_ALL_INT_LATCHED;
        break;

      default:
        *val = LSM6DSO_ALL_INT_PULSED;
        break;
    }

    ret = lsm6dso_mem_bank_set(ctx, LSM6DSO_EMBEDDED_FUNC_BANK);
  }

  if (ret == 0)
  {
    ret = lsm6dso_read_reg(ctx, LSM6DSO_PAGE_RW, (uint8_t *) &page_rw, 1);
  }

  if (ret == 0)
  {
    ret = lsm6dso_mem_bank_set(ctx, LSM6DSO_USER_BANK);
  }

  return ret;
}

/**
  * @}
  *
  */

/**
  * @defgroup  LSM6DSO_Wake_Up_event
  * @brief     This section groups all the functions that manage the Wake Up
  *            event generation.
  * @{
  *
  */

/**
  * @brief  Weight of 1 LSB of wakeup threshold.[set]
  *         0: 1 LSB =FS_XL  /  64
  *         1: 1 LSB = FS_XL / 256
  *
  * @param  ctx      read / write interface definitions
  * @param  val      change the values of wake_ths_w in
  *                                 reg WAKE_UP_DUR
  * @retval             interface status (MANDATORY: return 0 -> no Error)
  *
  */
int32_t lsm6dso_wkup_ths_weight_set(stmdev_ctx_t *ctx,
                                    lsm6dso_wake_ths_w_t val)
{
  lsm6dso_wake_up_dur_t reg;
  int32_t ret;

  ret = lsm6dso_read_reg(ctx, LSM6DSO_WAKE_UP_DUR, (uint8_t *)&reg, 1);

  if (ret == 0)
  {
    reg.wake_ths_w = (uint8_t)val;
    ret = lsm6dso_write_reg(ctx, LSM6DSO_WAKE_UP_DUR, (uint8_t *)&reg, 1);
  }

  return ret;
}

/**
  * @brief  Weight of 1 LSB of wakeup threshold.[get]
  *         0: 1 LSB =FS_XL  /  64
  *         1: 1 LSB = FS_XL / 256
  *
  * @param  ctx      read / write interface definitions
  * @param  val      Get the values of wake_ths_w in
  *                                 reg WAKE_UP_DUR
  * @retval             interface status (MANDATORY: return 0 -> no Error)
  *
  */
int32_t lsm6dso_wkup_ths_weight_get(stmdev_ctx_t *ctx,
                                    lsm6dso_wake_ths_w_t *val)
{
  lsm6dso_wake_up_dur_t reg;
  int32_t ret;

  ret = lsm6dso_read_reg(ctx, LSM6DSO_WAKE_UP_DUR, (uint8_t *)&reg, 1);

  switch (reg.wake_ths_w)
  {
    case LSM6DSO_LSb_FS_DIV_64:
      *val = LSM6DSO_LSb_FS_DIV_64;
      break;

    case LSM6DSO_LSb_FS_DIV_256:
      *val = LSM6DSO_LSb_FS_DIV_256;
      break;

    default:
      *val = LSM6DSO_LSb_FS_DIV_64;
      break;
  }

  return ret;
}

/**
  * @brief  Threshold for wakeup: 1 LSB weight depends on WAKE_THS_W in
  *         WAKE_UP_DUR.[set]
  *
  * @param  ctx      read / write interface definitions
  * @param  val      change the values of wk_ths in reg WAKE_UP_THS
  * @retval             interface status (MANDATORY: return 0 -> no Error)
  *
  */
int32_t lsm6dso_wkup_threshold_set(stmdev_ctx_t *ctx, uint8_t val)
{
  lsm6dso_wake_up_ths_t reg;
  int32_t ret;

  ret = lsm6dso_read_reg(ctx, LSM6DSO_WAKE_UP_THS, (uint8_t *)&reg, 1);

  if (ret == 0)
  {
    reg.wk_ths = val;
    ret = lsm6dso_write_reg(ctx, LSM6DSO_WAKE_UP_THS, (uint8_t *)&reg, 1);
  }

  return ret;
}

/**
  * @brief  Threshold for wakeup: 1 LSB weight depends on WAKE_THS_W in
  *         WAKE_UP_DUR.[get]
  *
  * @param  ctx      read / write interface definitions
  * @param  val      change the values of wk_ths in reg WAKE_UP_THS
  * @retval             interface status (MANDATORY: return 0 -> no Error)
  *
  */
int32_t lsm6dso_wkup_threshold_get(stmdev_ctx_t *ctx, uint8_t *val)
{
  lsm6dso_wake_up_ths_t reg;
  int32_t ret;

  ret = lsm6dso_read_reg(ctx, LSM6DSO_WAKE_UP_THS, (uint8_t *)&reg, 1);
  *val = reg.wk_ths;

  return ret;
}

/**
  * @brief  Wake up duration event.[set]
  *         1LSb = 1 / ODR
  *
  * @param  ctx      read / write interface definitions
  * @param  val      change the values of usr_off_on_wu in reg WAKE_UP_THS
  * @retval             interface status (MANDATORY: return 0 -> no Error)
  *
  */
int32_t lsm6dso_xl_usr_offset_on_wkup_set(stmdev_ctx_t *ctx,
                                          uint8_t val)
{
  lsm6dso_wake_up_ths_t reg;
  int32_t ret;

  ret = lsm6dso_read_reg(ctx, LSM6DSO_WAKE_UP_THS, (uint8_t *)&reg, 1);

  if (ret == 0)
  {
    reg.usr_off_on_wu = val;
    ret = lsm6dso_write_reg(ctx, LSM6DSO_WAKE_UP_THS, (uint8_t *)&reg, 1);
  }

  return ret;
}

/**
  * @brief  Wake up duration event.[get]
  *         1LSb = 1 / ODR
  *
  * @param  ctx      read / write interface definitions
  * @param  val      change the values of usr_off_on_wu in reg WAKE_UP_THS
  * @retval             interface status (MANDATORY: return 0 -> no Error)
  *
  */
int32_t lsm6dso_xl_usr_offset_on_wkup_get(stmdev_ctx_t *ctx,
                                          uint8_t *val)
{
  lsm6dso_wake_up_ths_t reg;
  int32_t ret;

  ret = lsm6dso_read_reg(ctx, LSM6DSO_WAKE_UP_THS, (uint8_t *)&reg, 1);
  *val = reg.usr_off_on_wu;

  return ret;
}
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
