sofiapanag/Shipwars-IoT-ESE-516/Code main/Code_main/WINC1500_HTTP_DOWNLOADER_EXAMPLE1/src/main.h

/**
 * \file
 *
 * \brief HTTP File Downloader Example.
 *
 * Copyright (c) 2016-2018 Microchip Technology Inc. and its subsidiaries.
 *
 * \asf_license_start
 *
 * \page License
 *
 * Subject to your compliance with these terms, you may use Microchip
 * software and any derivatives exclusively with Microchip products.
 * It is your responsibility to comply with third party license terms applicable
 * to your use of third party software (including open source software) that
 * may accompany Microchip software.
 *
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
 * \asf_license_stop
 *
 */

#ifndef MAIN_H_INCLUDED
#define MAIN_H_INCLUDED

#define MAX_SHIP 5
#define MAX_SHIP_SIZE 4
#define MAX_TILE 16


#ifdef __cplusplus
extern "C" {
#endif

#ifdef __cplusplus
}
#endif

#endif /* MAIN_H_INCLUDED */
