sofiapanag/Shipwars-IoT-ESE-516/Code main/Code_main/WINC1500_HTTP_DOWNLOADER_EXAMPLE1/src/SHTC3/SHTC3.h

/*
 * IncFile1.h
 *
 * Created: 4/30/2022 12:44:23 PM
 *  Author: Admin
 */ 


#ifndef SHTC3_H_
#define SHTC3_H_

#include <asf.h>
#include <FreeRTOS.h>

bool shtc_get(uint16_t *buf);


#endif /* INCFILE1_H_ */
