sofiapanag/Shipwars-IoT-ESE-516/Code main/Code_main/WINC1500_HTTP_DOWNLOADER_EXAMPLE1/src/WifiHandlerThread/WifiHandler.h

/**************************************************************************/ /**
 * @file      WifiHandler.h
 * @brief     File to handle HTTP Download and MQTT support
 * @author    Eduardo Garcia
 * @date      2020-01-01

 ******************************************************************************/

#pragma once

#pragma once
#ifdef __cplusplus
extern "C" {
#endif

/******************************************************************************
 * Includes
 ******************************************************************************/
#include "asf.h"

#include "MQTTClient/Wrapper/mqtt.h"
#include "SerialConsole.h"
#include "asf.h"
#include "driver/include/m2m_wifi.h"
#include "iot/http/http_client.h"
#include "main.h"
#include "socket/include/socket.h"
#include "stdio_serial.h"
/******************************************************************************
 * Defines
 ******************************************************************************/

#define WIFI_MQTT_INIT 0        ///< State for Wifi handler to Initialize MQTT Connection
#define WIFI_MQTT_HANDLE 1      ///< State for Wifi handler to Handle MQTT Connection
#define WIFI_DOWNLOAD_INIT 2    ///< State for Wifi handler to Initialize Download Connection
#define WIFI_DOWNLOAD_HANDLE 3  ///< State for Wifi handler to Handle Download Connection

#define WIFI_TASK_SIZE 1000
#define WIFI_PRIORITY (configMAX_PRIORITIES - 2)

/** Wi-Fi AP Settings. */
#define MAIN_WLAN_SSID "Soff :)"//"Kim's Home" "Mi 11"            /**< Destination SSID. Change to your WIFI SSID */
#define MAIN_WLAN_AUTH M2M_WIFI_SEC_WPA_PSK /**< Security manner */
#define MAIN_WLAN_PSK "sofiaa:)"//"25051997"  "87654321"          /**< Password for Destination SSID. Change to your password. Please dont hack my WiFi router */

/** IP address parsing. */
#define IPV4_BYTE(val, index) ((val >> (index * 8)) & 0xFF)

/** Content URI for download. */
#define MAIN_HTTP_FILE_URL "https://www.seas.upenn.edu/~pattana/fw.bin"  ///< Change me to the URL to download your OTAU binary file from!

/** Maximum size for packet buffer. */
#define MAIN_BUFFER_MAX_SIZE (512)
/** Maximum file name length. */
#define MAIN_MAX_FILE_NAME_LENGTH (64)
/** Maximum file extension length. */
#define MAIN_MAX_FILE_EXT_LENGTH (8)
/** Output format with '0'. */
#define MAIN_ZERO_FMT(SZ) (SZ == 4) ? "%04d" : (SZ == 3) ? "%03d" : (SZ == 2) ? "%02d" : "%d"
#define GAME_SIZE 20  ///< Number of plays in game

typedef enum {
    NOT_READY = 0,         /*!< Not ready. */
    STORAGE_READY = 0x01,  /*!< Storage is ready. */
    WIFI_CONNECTED = 0x02, /*!< Wi-Fi is connected. */
    GET_REQUESTED = 0x04,  /*!< GET request is sent. */
    DOWNLOADING = 0x08,    /*!< Running to download. */
    COMPLETED = 0x10,      /*!< Download completed. */
    CANCELED = 0x20        /*!< Download canceled. */
} download_state;

// Structure definition that holds IMU data
struct ImuDataPacket {
    int16_t xmg;
    int16_t ymg;
    int16_t zmg;
};

/* Max size of UART buffer. */
#define MAIN_CHAT_BUFFER_SIZE 64

/* Max size of MQTT buffer. */
#define MAIN_MQTT_BUFFER_SIZE 512
#define MAX_MQTT_MSG_SIZE 64

/* Limitation of user name. */
#define MAIN_CHAT_USER_NAME_SIZE 64


// Structure to hold a game packet
struct GameDataPacket {
	char game_msg[MAX_MQTT_MSG_SIZE];
	char game_TOPIC[20];
};


#define PLAYER1 1  ///< Comment me to compile for player 2. Uncomment me to define for player 1.

#ifdef PLAYER1
/* Chat MQTT topic. */
#define PLAYER 1
#define PLAYER_STR "1"
#define GAME_START_TOPIC_PUB "ESE516_T13_p1"
#define GAME_SHIPSIZE_TOPIC_SUB "ESE516_T13_shipsize_P1"
#define GAME_TURN_TOPIC_SUB "ESE516_T13_turn_P1"
#define CLOUDMQTT_USER_ID "rttyobe"			// Cloud MQTT User	

#else
/* Chat MQTT topic. */
#define PLAYER 2
#define PLAYER_STR "2"
#define GAME_START_TOPIC_PUB "ESE516_T13_p2"
#define GAME_SHIPSIZE_TOPIC_SUB "ESE516_T13_shipsize_P2"
#define GAME_TURN_TOPIC_SUB "ESE516_T13_turn_P2"
#define CLOUDMQTT_USER_ID "rttyobej"		// Cloud MQTT User	

#endif

#define GAME_SHIPLOC_TOPIC_PUB "ESE516_T13_loc"
#define GAME_FIRE_TOPIC_PUB "ESE516_T13_fire"

// Cloud MQTT pASSWORD
#define CLOUDMQTT_USER_PASSWORD "BrsJBNVoQBl7"

#define CLOUDMQTT_PORT 1883

/*
 * A MQTT broker server which was connected.
 * m2m.eclipse.org is public MQTT broker.
 */
static const char main_mqtt_broker[] = "broker.hivemq.com";

#define STRING_EOL "\r\n"
#define STRING_HEADER                                                                 \
    "-- HTTP file downloader example --" STRING_EOL "-- " BOARD_NAME " --" STRING_EOL \
    "-- Compiled: "__DATE__                                                           \
    " "__TIME__                                                                       \
    " --" STRING_EOL

/******************************************************************************
 * Structures and Enumerations
 ******************************************************************************/


/******************************************************************************
 * Global Function Declaration
 ******************************************************************************/
void vWifiTask(void *pvParameters);
void init_storage(void);
void WifiHandlerSetState(uint8_t state);

void SubscribeHandlerShipSizeTopic(MessageData *msgData);
void ConcatToArrString(uint8_t *arr, uint8_t arr_size, char* output);
void ConcatToArrStringInt(uint8_t *arr, char* output);
int WifiSendFireData(uint8_t *ship_loc, uint8_t loc_num);
int WifiSendPlaceData(uint8_t *ship_loc, uint8_t loc_num);
//int WifiSendGameData(uint8_t *ship_loc, uint8_t loc_num, char* TOPIC);
//int WifiSendGameDataInt(uint8_t *ship_loc, uint8_t loc_num);

void configure_extint_channel(void);
void configure_extint_callbacks(void);

#ifdef __cplusplus
}
#endif
